tejeez/geckokapula/gecko_sdk_suite/v2.7/platform/Device/SiliconLabs/BGM1/Include/bgm1_adc.h

/***************************************************************************//**
 * @file
 * @brief BGM1_ADC register and bit field definitions
 *******************************************************************************
 * # License
 * <b>Copyright 2020 Silicon Laboratories Inc. www.silabs.com</b>
 *******************************************************************************
 *
 * SPDX-License-Identifier: Zlib
 *
 * The licensor of this software is Silicon Laboratories Inc.
 *
 * This software is provided 'as-is', without any express or implied
 * warranty. In no event will the authors be held liable for any damages
 * arising from the use of this software.
 *
 * Permission is granted to anyone to use this software for any purpose,
 * including commercial applications, and to alter it and redistribute it
 * freely, subject to the following restrictions:
 *
 * 1. The origin of this software must not be misrepresented; you must not
 *    claim that you wrote the original software. If you use this software
 *    in a product, an acknowledgment in the product documentation would be
 *    appreciated but is not required.
 * 2. Altered source versions must be plainly marked as such, and must not be
 *    misrepresented as being the original software.
 * 3. This notice may not be removed or altered from any source distribution.
 *
 ******************************************************************************/

#if defined(__ICCARM__)
#pragma system_include       /* Treat file as system include file. */
#elif defined(__ARMCC_VERSION) && (__ARMCC_VERSION >= 6010050)
#pragma clang system_header  /* Treat file as system include file. */
#endif

/***************************************************************************//**
 * @addtogroup Parts
 * @{
 ******************************************************************************/
/***************************************************************************//**
 * @defgroup BGM1_ADC ADC
 * @{
 * @brief BGM1_ADC Register Declaration
 ******************************************************************************/
/** ADC Register Declaration */
typedef struct {
  __IOM uint32_t CTRL;            /**< Control Register  */
  uint32_t       RESERVED0[1U];   /**< Reserved for future use **/
  __IOM uint32_t CMD;             /**< Command Register  */
  __IM uint32_t  STATUS;          /**< Status Register  */
  __IOM uint32_t SINGLECTRL;      /**< Single Channel Control Register  */
  __IOM uint32_t SINGLECTRLX;     /**< Single Channel Control Register Continued  */
  __IOM uint32_t SCANCTRL;        /**< Scan Control Register  */
  __IOM uint32_t SCANCTRLX;       /**< Scan Control Register Continued  */
  __IOM uint32_t SCANMASK;        /**< Scan Sequence Input Mask Register  */
  __IOM uint32_t SCANINPUTSEL;    /**< Input Selection Register for Scan Mode  */
  __IOM uint32_t SCANNEGSEL;      /**< Negative Input Select Register for Scan  */
  __IOM uint32_t CMPTHR;          /**< Compare Threshold Register  */
  __IOM uint32_t BIASPROG;        /**< Bias Programming Register for Various Analog Blocks Used in ADC Operation  */
  __IOM uint32_t CAL;             /**< Calibration Register  */
  __IM uint32_t  IF;              /**< Interrupt Flag Register  */
  __IOM uint32_t IFS;             /**< Interrupt Flag Set Register  */
  __IOM uint32_t IFC;             /**< Interrupt Flag Clear Register  */
  __IOM uint32_t IEN;             /**< Interrupt Enable Register  */
  __IM uint32_t  SINGLEDATA;      /**< Single Conversion Result Data  */
  __IM uint32_t  SCANDATA;        /**< Scan Conversion Result Data  */
  __IM uint32_t  SINGLEDATAP;     /**< Single Conversion Result Data Peek Register  */
  __IM uint32_t  SCANDATAP;       /**< Scan Sequence Result Data Peek Register  */
  uint32_t       RESERVED1[4U];   /**< Reserved for future use **/
  __IM uint32_t  SCANDATAX;       /**< Scan Sequence Result Data + Data Source Register  */
  __IM uint32_t  SCANDATAXP;      /**< Scan Sequence Result Data + Data Source Peek Register  */

  uint32_t       RESERVED2[3U];   /**< Reserved for future use **/
  __IM uint32_t  APORTREQ;        /**< APORT Request Status Register  */
  __IM uint32_t  APORTCONFLICT;   /**< APORT Conflict Status Register  */
  __IM uint32_t  SINGLEFIFOCOUNT; /**< Single FIFO Count Register  */
  __IM uint32_t  SCANFIFOCOUNT;   /**< Scan FIFO Count Register  */
  __IOM uint32_t SINGLEFIFOCLEAR; /**< Single FIFO Clear Register  */
  __IOM uint32_t SCANFIFOCLEAR;   /**< Scan FIFO Clear Register  */
  __IOM uint32_t APORTMASTERDIS;  /**< APORT Bus Master Disable Register  */
} ADC_TypeDef;                    /** @} */

/***************************************************************************//**
 * @addtogroup BGM1_ADC
 * @{
 * @defgroup BGM1_ADC_BitFields  ADC Bit Fields
 * @{
 ******************************************************************************/

/* Bit fields for ADC CTRL */
#define _ADC_CTRL_RESETVALUE                               0x001F0000UL                              /**< Default value for ADC_CTRL */
#define _ADC_CTRL_MASK                                     0x2F7F7FDFUL                              /**< Mask for ADC_CTRL */
#define _ADC_CTRL_WARMUPMODE_SHIFT                         0                                         /**< Shift value for ADC_WARMUPMODE */
#define _ADC_CTRL_WARMUPMODE_MASK                          0x3UL                                     /**< Bit mask for ADC_WARMUPMODE */
#define _ADC_CTRL_WARMUPMODE_DEFAULT                       0x00000000UL                              /**< Mode DEFAULT for ADC_CTRL */
#define _ADC_CTRL_WARMUPMODE_NORMAL                        0x00000000UL                              /**< Mode NORMAL for ADC_CTRL */
#define _ADC_CTRL_WARMUPMODE_KEEPINSTANDBY                 0x00000001UL                              /**< Mode KEEPINSTANDBY for ADC_CTRL */
#define _ADC_CTRL_WARMUPMODE_KEEPINSLOWACC                 0x00000002UL                              /**< Mode KEEPINSLOWACC for ADC_CTRL */
#define _ADC_CTRL_WARMUPMODE_KEEPADCWARM                   0x00000003UL                              /**< Mode KEEPADCWARM for ADC_CTRL */
#define ADC_CTRL_WARMUPMODE_DEFAULT                        (_ADC_CTRL_WARMUPMODE_DEFAULT << 0)       /**< Shifted mode DEFAULT for ADC_CTRL */
#define ADC_CTRL_WARMUPMODE_NORMAL                         (_ADC_CTRL_WARMUPMODE_NORMAL << 0)        /**< Shifted mode NORMAL for ADC_CTRL */
#define ADC_CTRL_WARMUPMODE_KEEPINSTANDBY                  (_ADC_CTRL_WARMUPMODE_KEEPINSTANDBY << 0) /**< Shifted mode KEEPINSTANDBY for ADC_CTRL */
#define ADC_CTRL_WARMUPMODE_KEEPINSLOWACC                  (_ADC_CTRL_WARMUPMODE_KEEPINSLOWACC << 0) /**< Shifted mode KEEPINSLOWACC for ADC_CTRL */
#define ADC_CTRL_WARMUPMODE_KEEPADCWARM                    (_ADC_CTRL_WARMUPMODE_KEEPADCWARM << 0)   /**< Shifted mode KEEPADCWARM for ADC_CTRL */
#define ADC_CTRL_SINGLEDMAWU                               (0x1UL << 2)                              /**< SINGLEFIFO DMA Wakeup */
#define _ADC_CTRL_SINGLEDMAWU_SHIFT                        2                                         /**< Shift value for ADC_SINGLEDMAWU */
#define _ADC_CTRL_SINGLEDMAWU_MASK                         0x4UL                                     /**< Bit mask for ADC_SINGLEDMAWU */
#define _ADC_CTRL_SINGLEDMAWU_DEFAULT                      0x00000000UL                              /**< Mode DEFAULT for ADC_CTRL */
#define ADC_CTRL_SINGLEDMAWU_DEFAULT                       (_ADC_CTRL_SINGLEDMAWU_DEFAULT << 2)      /**< Shifted mode DEFAULT for ADC_CTRL */
#define ADC_CTRL_SCANDMAWU                                 (0x1UL << 3)                              /**< SCANFIFO DMA Wakeup */
#define _ADC_CTRL_SCANDMAWU_SHIFT                          3                                         /**< Shift value for ADC_SCANDMAWU */
#define _ADC_CTRL_SCANDMAWU_MASK                           0x8UL                                     /**< Bit mask for ADC_SCANDMAWU */
#define _ADC_CTRL_SCANDMAWU_DEFAULT                        0x00000000UL                              /**< Mode DEFAULT for ADC_CTRL */
#define ADC_CTRL_SCANDMAWU_DEFAULT                         (_ADC_CTRL_SCANDMAWU_DEFAULT << 3)        /**< Shifted mode DEFAULT for ADC_CTRL */
#define ADC_CTRL_TAILGATE                                  (0x1UL << 4)                              /**< Conversion Tailgating */
#define _ADC_CTRL_TAILGATE_SHIFT                           4                                         /**< Shift value for ADC_TAILGATE */
#define _ADC_CTRL_TAILGATE_MASK                            0x10UL                                    /**< Bit mask for ADC_TAILGATE */
#define _ADC_CTRL_TAILGATE_DEFAULT                         0x00000000UL                              /**< Mode DEFAULT for ADC_CTRL */
#define ADC_CTRL_TAILGATE_DEFAULT                          (_ADC_CTRL_TAILGATE_DEFAULT << 4)         /**< Shifted mode DEFAULT for ADC_CTRL */
#define ADC_CTRL_ASYNCCLKEN                                (0x1UL << 6)                              /**< Selects ASYNC CLK Enable Mode When ADCCLKMODE=1 */
#define _ADC_CTRL_ASYNCCLKEN_SHIFT                         6                                         /**< Shift value for ADC_ASYNCCLKEN */
#define _ADC_CTRL_ASYNCCLKEN_MASK                          0x40UL                                    /**< Bit mask for ADC_ASYNCCLKEN */
#define _ADC_CTRL_ASYNCCLKEN_DEFAULT                       0x00000000UL                              /**< Mode DEFAULT for ADC_CTRL */
#define _ADC_CTRL_ASYNCCLKEN_ASNEEDED                      0x00000000UL                              /**< Mode ASNEEDED for ADC_CTRL */
#define _ADC_CTRL_ASYNCCLKEN_ALWAYSON                      0x00000001UL                              /**< Mode ALWAYSON for ADC_CTRL */
#define ADC_CTRL_ASYNCCLKEN_DEFAULT                        (_ADC_CTRL_ASYNCCLKEN_DEFAULT << 6)       /**< Shifted mode DEFAULT for ADC_CTRL */
#define ADC_CTRL_ASYNCCLKEN_ASNEEDED                       (_ADC_CTRL_ASYNCCLKEN_ASNEEDED << 6)      /**< Shifted mode ASNEEDED for ADC_CTRL */
#define ADC_CTRL_ASYNCCLKEN_ALWAYSON                       (_ADC_CTRL_ASYNCCLKEN_ALWAYSON << 6)      /**< Shifted mode ALWAYSON for ADC_CTRL */
#define ADC_CTRL_ADCCLKMODE                                (0x1UL << 7)                              /**< ADC Clock Mode */
#define _ADC_CTRL_ADCCLKMODE_SHIFT                         7                                         /**< Shift value for ADC_ADCCLKMODE */
#define _ADC_CTRL_ADCCLKMODE_MASK                          0x80UL                                    /**< Bit mask for ADC_ADCCLKMODE */
#define _ADC_CTRL_ADCCLKMODE_DEFAULT                       0x00000000UL                              /**< Mode DEFAULT for ADC_CTRL */
#define _ADC_CTRL_ADCCLKMODE_SYNC                          0x00000000UL                              /**< Mode SYNC for ADC_CTRL */
#define _ADC_CTRL_ADCCLKMODE_ASYNC                         0x00000001UL                              /**< Mode ASYNC for ADC_CTRL */
#define ADC_CTRL_ADCCLKMODE_DEFAULT                        (_ADC_CTRL_ADCCLKMODE_DEFAULT << 7)       /**< Shifted mode DEFAULT for ADC_CTRL */
#define ADC_CTRL_ADCCLKMODE_SYNC                           (_ADC_CTRL_ADCCLKMODE_SYNC << 7)          /**< Shifted mode SYNC for ADC_CTRL */
#define ADC_CTRL_ADCCLKMODE_ASYNC                          (_ADC_CTRL_ADCCLKMODE_ASYNC << 7)         /**< Shifted mode ASYNC for ADC_CTRL */
#define _ADC_CTRL_PRESC_SHIFT                              8                                         /**< Shift value for ADC_PRESC */
#define _ADC_CTRL_PRESC_MASK                               0x7F00UL                                  /**< Bit mask for ADC_PRESC */
#define _ADC_CTRL_PRESC_DEFAULT                            0x00000000UL                              /**< Mode DEFAULT for ADC_CTRL */
#define _ADC_CTRL_PRESC_NODIVISION                         0x00000000UL                              /**< Mode NODIVISION for ADC_CTRL */
#define ADC_CTRL_PRESC_DEFAULT                             (_ADC_CTRL_PRESC_DEFAULT << 8)            /**< Shifted mode DEFAULT for ADC_CTRL */
#define ADC_CTRL_PRESC_NODIVISION                          (_ADC_CTRL_PRESC_NODIVISION << 8)         /**< Shifted mode NODIVISION for ADC_CTRL */
#define _ADC_CTRL_TIMEBASE_SHIFT                           16                                        /**< Shift value for ADC_TIMEBASE */
#define _ADC_CTRL_TIMEBASE_MASK                            0x7F0000UL                                /**< Bit mask for ADC_TIMEBASE */
#define _ADC_CTRL_TIMEBASE_DEFAULT                         0x0000001FUL                              /**< Mode DEFAULT for ADC_CTRL */
#define ADC_CTRL_TIMEBASE_DEFAULT                          (_ADC_CTRL_TIMEBASE_DEFAULT << 16)        /**< Shifted mode DEFAULT for ADC_CTRL */
#define _ADC_CTRL_OVSRSEL_SHIFT                            24                                        /**< Shift value for ADC_OVSRSEL */
#define _ADC_CTRL_OVSRSEL_MASK                             0xF000000UL                               /**< Bit mask for ADC_OVSRSEL */
#define _ADC_CTRL_OVSRSEL_DEFAULT                          0x00000000UL                              /**< Mode DEFAULT for ADC_CTRL */
#define _ADC_CTRL_OVSRSEL_X2                               0x00000000UL                              /**< Mode X2 for ADC_CTRL */
#define _ADC_CTRL_OVSRSEL_X4                               0x00000001UL                              /**< Mode X4 for ADC_CTRL */
#define _ADC_CTRL_OVSRSEL_X8                               0x00000002UL                              /**< Mode X8 for ADC_CTRL */
#define _ADC_CTRL_OVSRSEL_X16                              0x00000003UL                              /**< Mode X16 for ADC_CTRL */
#define _ADC_CTRL_OVSRSEL_X32                              0x00000004UL                              /**< Mode X32 for ADC_CTRL */
#define _ADC_CTRL_OVSRSEL_X64                              0x00000005UL                              /**< Mode X64 for ADC_CTRL */
#define _ADC_CTRL_OVSRSEL_X128                             0x00000006UL                              /**< Mode X128 for ADC_CTRL */
#define _ADC_CTRL_OVSRSEL_X256                             0x00000007UL                              /**< Mode X256 for ADC_CTRL */
#define _ADC_CTRL_OVSRSEL_X512                             0x00000008UL                              /**< Mode X512 for ADC_CTRL */
#define _ADC_CTRL_OVSRSEL_X1024                            0x00000009UL                              /**< Mode X1024 for ADC_CTRL */
#define _ADC_CTRL_OVSRSEL_X2048                            0x0000000AUL                              /**< Mode X2048 for ADC_CTRL */
#define _ADC_CTRL_OVSRSEL_X4096                            0x0000000BUL                              /**< Mode X4096 for ADC_CTRL */
#define ADC_CTRL_OVSRSEL_DEFAULT                           (_ADC_CTRL_OVSRSEL_DEFAULT << 24)         /**< Shifted mode DEFAULT for ADC_CTRL */
#define ADC_CTRL_OVSRSEL_X2                                (_ADC_CTRL_OVSRSEL_X2 << 24)              /**< Shifted mode X2 for ADC_CTRL */
#define ADC_CTRL_OVSRSEL_X4                                (_ADC_CTRL_OVSRSEL_X4 << 24)              /**< Shifted mode X4 for ADC_CTRL */
#define ADC_CTRL_OVSRSEL_X8                                (_ADC_CTRL_OVSRSEL_X8 << 24)              /**< Shifted mode X8 for ADC_CTRL */
#define ADC_CTRL_OVSRSEL_X16                               (_ADC_CTRL_OVSRSEL_X16 << 24)             /**< Shifted mode X16 for ADC_CTRL */
#define ADC_CTRL_OVSRSEL_X32                               (_ADC_CTRL_OVSRSEL_X32 << 24)             /**< Shifted mode X32 for ADC_CTRL */
#define ADC_CTRL_OVSRSEL_X64                               (_ADC_CTRL_OVSRSEL_X64 << 24)             /**< Shifted mode X64 for ADC_CTRL */
#define ADC_CTRL_OVSRSEL_X128                              (_ADC_CTRL_OVSRSEL_X128 << 24)            /**< Shifted mode X128 for ADC_CTRL */
#define ADC_CTRL_OVSRSEL_X256                              (_ADC_CTRL_OVSRSEL_X256 << 24)            /**< Shifted mode X256 for ADC_CTRL */
#define ADC_CTRL_OVSRSEL_X512                              (_ADC_CTRL_OVSRSEL_X512 << 24)            /**< Shifted mode X512 for ADC_CTRL */
#define ADC_CTRL_OVSRSEL_X1024                             (_ADC_CTRL_OVSRSEL_X1024 << 24)           /**< Shifted mode X1024 for ADC_CTRL */
#define ADC_CTRL_OVSRSEL_X2048                             (_ADC_CTRL_OVSRSEL_X2048 << 24)           /**< Shifted mode X2048 for ADC_CTRL */
#define ADC_CTRL_OVSRSEL_X4096                             (_ADC_CTRL_OVSRSEL_X4096 << 24)           /**< Shifted mode X4096 for ADC_CTRL */
#define ADC_CTRL_CHCONMODE                                 (0x1UL << 29)                             /**< Channel Connect */
#define _ADC_CTRL_CHCONMODE_SHIFT                          29                                        /**< Shift value for ADC_CHCONMODE */
#define _ADC_CTRL_CHCONMODE_MASK                           0x20000000UL                              /**< Bit mask for ADC_CHCONMODE */
#define _ADC_CTRL_CHCONMODE_DEFAULT                        0x00000000UL                              /**< Mode DEFAULT for ADC_CTRL */
#define _ADC_CTRL_CHCONMODE_MAXSETTLE                      0x00000000UL                              /**< Mode MAXSETTLE for ADC_CTRL */
#define _ADC_CTRL_CHCONMODE_MAXRESP                        0x00000001UL                              /**< Mode MAXRESP for ADC_CTRL */
#define ADC_CTRL_CHCONMODE_DEFAULT                         (_ADC_CTRL_CHCONMODE_DEFAULT << 29)       /**< Shifted mode DEFAULT for ADC_CTRL */
#define ADC_CTRL_CHCONMODE_MAXSETTLE                       (_ADC_CTRL_CHCONMODE_MAXSETTLE << 29)     /**< Shifted mode MAXSETTLE for ADC_CTRL */
#define ADC_CTRL_CHCONMODE_MAXRESP                         (_ADC_CTRL_CHCONMODE_MAXRESP << 29)       /**< Shifted mode MAXRESP for ADC_CTRL */

/* Bit fields for ADC CMD */
#define _ADC_CMD_RESETVALUE                                0x00000000UL                        /**< Default value for ADC_CMD */
#define _ADC_CMD_MASK                                      0x0000000FUL                        /**< Mask for ADC_CMD */
#define ADC_CMD_SINGLESTART                                (0x1UL << 0)                        /**< Single Channel Conversion Start */
#define _ADC_CMD_SINGLESTART_SHIFT                         0                                   /**< Shift value for ADC_SINGLESTART */
#define _ADC_CMD_SINGLESTART_MASK                          0x1UL                               /**< Bit mask for ADC_SINGLESTART */
#define _ADC_CMD_SINGLESTART_DEFAULT                       0x00000000UL                        /**< Mode DEFAULT for ADC_CMD */
#define ADC_CMD_SINGLESTART_DEFAULT                        (_ADC_CMD_SINGLESTART_DEFAULT << 0) /**< Shifted mode DEFAULT for ADC_CMD */
#define ADC_CMD_SINGLESTOP                                 (0x1UL << 1)                        /**< Single Channel Conversion Stop */
#define _ADC_CMD_SINGLESTOP_SHIFT                          1                                   /**< Shift value for ADC_SINGLESTOP */
#define _ADC_CMD_SINGLESTOP_MASK                           0x2UL                               /**< Bit mask for ADC_SINGLESTOP */
#define _ADC_CMD_SINGLESTOP_DEFAULT                        0x00000000UL                        /**< Mode DEFAULT for ADC_CMD */
#define ADC_CMD_SINGLESTOP_DEFAULT                         (_ADC_CMD_SINGLESTOP_DEFAULT << 1)  /**< Shifted mode DEFAULT for ADC_CMD */
#define ADC_CMD_SCANSTART                                  (0x1UL << 2)                        /**< Scan Sequence Start */
#define _ADC_CMD_SCANSTART_SHIFT                           2                                   /**< Shift value for ADC_SCANSTART */
#define _ADC_CMD_SCANSTART_MASK                            0x4UL                               /**< Bit mask for ADC_SCANSTART */
#define _ADC_CMD_SCANSTART_DEFAULT                         0x00000000UL                        /**< Mode DEFAULT for ADC_CMD */
#define ADC_CMD_SCANSTART_DEFAULT                          (_ADC_CMD_SCANSTART_DEFAULT << 2)   /**< Shifted mode DEFAULT for ADC_CMD */
#define ADC_CMD_SCANSTOP                                   (0x1UL << 3)                        /**< Scan Sequence Stop */
#define _ADC_CMD_SCANSTOP_SHIFT                            3                                   /**< Shift value for ADC_SCANSTOP */
#define _ADC_CMD_SCANSTOP_MASK                             0x8UL                               /**< Bit mask for ADC_SCANSTOP */
#define _ADC_CMD_SCANSTOP_DEFAULT                          0x00000000UL                        /**< Mode DEFAULT for ADC_CMD */
#define ADC_CMD_SCANSTOP_DEFAULT                           (_ADC_CMD_SCANSTOP_DEFAULT << 3)    /**< Shifted mode DEFAULT for ADC_CMD */

/* Bit fields for ADC STATUS */
#define _ADC_STATUS_RESETVALUE                             0x00000000UL                             /**< Default value for ADC_STATUS */
#define _ADC_STATUS_MASK                                   0x00031F03UL                             /**< Mask for ADC_STATUS */
#define ADC_STATUS_SINGLEACT                               (0x1UL << 0)                             /**< Single Channel Conversion Active */
#define _ADC_STATUS_SINGLEACT_SHIFT                        0                                        /**< Shift value for ADC_SINGLEACT */
#define _ADC_STATUS_SINGLEACT_MASK                         0x1UL                                    /**< Bit mask for ADC_SINGLEACT */
#define _ADC_STATUS_SINGLEACT_DEFAULT                      0x00000000UL                             /**< Mode DEFAULT for ADC_STATUS */
#define ADC_STATUS_SINGLEACT_DEFAULT                       (_ADC_STATUS_SINGLEACT_DEFAULT << 0)     /**< Shifted mode DEFAULT for ADC_STATUS */
#define ADC_STATUS_SCANACT                                 (0x1UL << 1)                             /**< Scan Conversion Active */
#define _ADC_STATUS_SCANACT_SHIFT                          1                                        /**< Shift value for ADC_SCANACT */
#define _ADC_STATUS_SCANACT_MASK                           0x2UL                                    /**< Bit mask for ADC_SCANACT */
#define _ADC_STATUS_SCANACT_DEFAULT                        0x00000000UL                             /**< Mode DEFAULT for ADC_STATUS */
#define ADC_STATUS_SCANACT_DEFAULT                         (_ADC_STATUS_SCANACT_DEFAULT << 1)       /**< Shifted mode DEFAULT for ADC_STATUS */
#define ADC_STATUS_SINGLEREFWARM                           (0x1UL << 8)                             /**< Single Channel Reference Warmed Up */
#define _ADC_STATUS_SINGLEREFWARM_SHIFT                    8                                        /**< Shift value for ADC_SINGLEREFWARM */
#define _ADC_STATUS_SINGLEREFWARM_MASK                     0x100UL                                  /**< Bit mask for ADC_SINGLEREFWARM */
#define _ADC_STATUS_SINGLEREFWARM_DEFAULT                  0x00000000UL                             /**< Mode DEFAULT for ADC_STATUS */
#define ADC_STATUS_SINGLEREFWARM_DEFAULT                   (_ADC_STATUS_SINGLEREFWARM_DEFAULT << 8) /**< Shifted mode DEFAULT for ADC_STATUS */
#define ADC_STATUS_SCANREFWARM                             (0x1UL << 9)                             /**< Scan Reference Warmed Up */
#define _ADC_STATUS_SCANREFWARM_SHIFT                      9                                        /**< Shift value for ADC_SCANREFWARM */
#define _ADC_STATUS_SCANREFWARM_MASK                       0x200UL                                  /**< Bit mask for ADC_SCANREFWARM */
#define _ADC_STATUS_SCANREFWARM_DEFAULT                    0x00000000UL                             /**< Mode DEFAULT for ADC_STATUS */
#define ADC_STATUS_SCANREFWARM_DEFAULT                     (_ADC_STATUS_SCANREFWARM_DEFAULT << 9)   /**< Shifted mode DEFAULT for ADC_STATUS */
#define _ADC_STATUS_PROGERR_SHIFT                          10                                       /**< Shift value for ADC_PROGERR */
#define _ADC_STATUS_PROGERR_MASK                           0xC00UL                                  /**< Bit mask for ADC_PROGERR */
#define _ADC_STATUS_PROGERR_DEFAULT                        0x00000000UL                             /**< Mode DEFAULT for ADC_STATUS */
#define _ADC_STATUS_PROGERR_BUSCONF                        0x00000001UL                             /**< Mode BUSCONF for ADC_STATUS */
#define _ADC_STATUS_PROGERR_NEGSELCONF                     0x00000002UL                             /**< Mode NEGSELCONF for ADC_STATUS */
#define ADC_STATUS_PROGERR_DEFAULT                         (_ADC_STATUS_PROGERR_DEFAULT << 10)      /**< Shifted mode DEFAULT for ADC_STATUS */
#define ADC_STATUS_PROGERR_BUSCONF                         (_ADC_STATUS_PROGERR_BUSCONF << 10)      /**< Shifted mode BUSCONF for ADC_STATUS */
#define ADC_STATUS_PROGERR_NEGSELCONF                      (_ADC_STATUS_PROGERR_NEGSELCONF << 10)   /**< Shifted mode NEGSELCONF for ADC_STATUS */
#define ADC_STATUS_WARM                                    (0x1UL << 12)                            /**< ADC Warmed Up */
#define _ADC_STATUS_WARM_SHIFT                             12                                       /**< Shift value for ADC_WARM */
#define _ADC_STATUS_WARM_MASK                              0x1000UL                                 /**< Bit mask for ADC_WARM */
#define _ADC_STATUS_WARM_DEFAULT                           0x00000000UL                             /**< Mode DEFAULT for ADC_STATUS */
#define ADC_STATUS_WARM_DEFAULT                            (_ADC_STATUS_WARM_DEFAULT << 12)         /**< Shifted mode DEFAULT for ADC_STATUS */
#define ADC_STATUS_SINGLEDV                                (0x1UL << 16)                            /**< Single Channel Data Valid */
#define _ADC_STATUS_SINGLEDV_SHIFT                         16                                       /**< Shift value for ADC_SINGLEDV */
#define _ADC_STATUS_SINGLEDV_MASK                          0x10000UL                                /**< Bit mask for ADC_SINGLEDV */
#define _ADC_STATUS_SINGLEDV_DEFAULT                       0x00000000UL                             /**< Mode DEFAULT for ADC_STATUS */
#define ADC_STATUS_SINGLEDV_DEFAULT                        (_ADC_STATUS_SINGLEDV_DEFAULT << 16)     /**< Shifted mode DEFAULT for ADC_STATUS */
#define ADC_STATUS_SCANDV                                  (0x1UL << 17)                            /**< Scan Data Valid */
#define _ADC_STATUS_SCANDV_SHIFT                           17                                       /**< Shift value for ADC_SCANDV */
#define _ADC_STATUS_SCANDV_MASK                            0x20000UL                                /**< Bit mask for ADC_SCANDV */
#define _ADC_STATUS_SCANDV_DEFAULT                         0x00000000UL                             /**< Mode DEFAULT for ADC_STATUS */
#define ADC_STATUS_SCANDV_DEFAULT                          (_ADC_STATUS_SCANDV_DEFAULT << 17)       /**< Shifted mode DEFAULT for ADC_STATUS */

/* Bit fields for ADC SINGLECTRL */
#define _ADC_SINGLECTRL_RESETVALUE                         0x00FFFF00UL                               /**< Default value for ADC_SINGLECTRL */
#define _ADC_SINGLECTRL_MASK                               0xAFFFFFFFUL                               /**< Mask for ADC_SINGLECTRL */
#define ADC_SINGLECTRL_REP                                 (0x1UL << 0)                               /**< Single Channel Repetitive Mode */
#define _ADC_SINGLECTRL_REP_SHIFT                          0                                          /**< Shift value for ADC_REP */
#define _ADC_SINGLECTRL_REP_MASK                           0x1UL                                      /**< Bit mask for ADC_REP */
#define _ADC_SINGLECTRL_REP_DEFAULT                        0x00000000UL                               /**< Mode DEFAULT for ADC_SINGLECTRL */
#define ADC_SINGLECTRL_REP_DEFAULT                         (_ADC_SINGLECTRL_REP_DEFAULT << 0)         /**< Shifted mode DEFAULT for ADC_SINGLECTRL */
#define ADC_SINGLECTRL_DIFF                                (0x1UL << 1)                               /**< Single Channel Differential Mode */
#define _ADC_SINGLECTRL_DIFF_SHIFT                         1                                          /**< Shift value for ADC_DIFF */
#define _ADC_SINGLECTRL_DIFF_MASK                          0x2UL                                      /**< Bit mask for ADC_DIFF */
#define _ADC_SINGLECTRL_DIFF_DEFAULT                       0x00000000UL                               /**< Mode DEFAULT for ADC_SINGLECTRL */
#define ADC_SINGLECTRL_DIFF_DEFAULT                        (_ADC_SINGLECTRL_DIFF_DEFAULT << 1)        /**< Shifted mode DEFAULT for ADC_SINGLECTRL */
#define ADC_SINGLECTRL_ADJ                                 (0x1UL << 2)                               /**< Single Channel Result Adjustment */
#define _ADC_SINGLECTRL_ADJ_SHIFT                          2                                          /**< Shift value for ADC_ADJ */
#define _ADC_SINGLECTRL_ADJ_MASK                           0x4UL                                      /**< Bit mask for ADC_ADJ */
#define _ADC_SINGLECTRL_ADJ_DEFAULT                        0x00000000UL                               /**< Mode DEFAULT for ADC_SINGLECTRL */
#define _ADC_SINGLECTRL_ADJ_RIGHT                          0x00000000UL                               /**< Mode RIGHT for ADC_SINGLECTRL */
#define _ADC_SINGLECTRL_ADJ_LEFT                           0x00000001UL                               /**< Mode LEFT for ADC_SINGLECTRL */
#define ADC_SINGLECTRL_ADJ_DEFAULT                         (_ADC_SINGLECTRL_ADJ_DEFAULT << 2)         /**< Shifted mode DEFAULT for ADC_SINGLECTRL */
#define ADC_SINGLECTRL_ADJ_RIGHT                           (_ADC_SINGLECTRL_ADJ_RIGHT << 2)           /**< Shifted mode RIGHT for ADC_SINGLECTRL */
#define ADC_SINGLECTRL_ADJ_LEFT                            (_ADC_SINGLECTRL_ADJ_LEFT << 2)            /**< Shifted mode LEFT for ADC_SINGLECTRL */
#define _ADC_SINGLECTRL_RES_SHIFT                          3                                          /**< Shift value for ADC_RES */
#define _ADC_SINGLECTRL_RES_MASK                           0x18UL                                     /**< Bit mask for ADC_RES */
#define _ADC_SINGLECTRL_RES_DEFAULT                        0x00000000UL                               /**< Mode DEFAULT for ADC_SINGLECTRL */
#define _ADC_SINGLECTRL_RES_12BIT                          0x00000000UL                               /**< Mode 12BIT for ADC_SINGLECTRL */
#define _ADC_SINGLECTRL_RES_8BIT                           0x00000001UL                               /**< Mode 8BIT for ADC_SINGLECTRL */
#define _ADC_SINGLECTRL_RES_6BIT                           0x00000002UL                               /**< Mode 6BIT for ADC_SINGLECTRL */
#define _ADC_SINGLECTRL_RES_OVS                            0x00000003UL                               /**< Mode OVS for ADC_SINGLECTRL */
#define ADC_SINGLECTRL_RES_DEFAULT                         (_ADC_SINGLECTRL_RES_DEFAULT << 3)         /**< Shifted mode DEFAULT for ADC_SINGLECTRL */
#define ADC_SINGLECTRL_RES_12BIT                           (_ADC_SINGLECTRL_RES_12BIT << 3)           /**< Shifted mode 12BIT for ADC_SINGLECTRL */
#define ADC_SINGLECTRL_RES_8BIT                            (_ADC_SINGLECTRL_RES_8BIT << 3)            /**< Shifted mode 8BIT for ADC_SINGLECTRL */
#define ADC_SINGLECTRL_RES_6BIT                            (_ADC_SINGLECTRL_RES_6BIT << 3)            /**< Shifted mode 6BIT for ADC_SINGLECTRL */
#define ADC_SINGLECTRL_RES_OVS                             (_ADC_SINGLECTRL_RES_OVS << 3)             /**< Shifted mode OVS for ADC_SINGLECTRL */
#define _ADC_SINGLECTRL_REF_SHIFT                          5                                          /**< Shift value for ADC_REF */
#define _ADC_SINGLECTRL_REF_MASK                           0xE0UL                                     /**< Bit mask for ADC_REF */
#define _ADC_SINGLECTRL_REF_DEFAULT                        0x00000000UL                               /**< Mode DEFAULT for ADC_SINGLECTRL */
#define _ADC_SINGLECTRL_REF_1V25                           0x00000000UL                               /**< Mode 1V25 for ADC_SINGLECTRL */
#define _ADC_SINGLECTRL_REF_2V5                            0x00000001UL                               /**< Mode 2V5 for ADC_SINGLECTRL */
#define _ADC_SINGLECTRL_REF_VDD                            0x00000002UL                               /**< Mode VDD for ADC_SINGLECTRL */
#define _ADC_SINGLECTRL_REF_5V                             0x00000003UL                               /**< Mode 5V for ADC_SINGLECTRL */
#define _ADC_SINGLECTRL_REF_EXTSINGLE                      0x00000004UL                               /**< Mode EXTSINGLE for ADC_SINGLECTRL */
#define _ADC_SINGLECTRL_REF_2XEXTDIFF                      0x00000005UL                               /**< Mode 2XEXTDIFF for ADC_SINGLECTRL */
#define _ADC_SINGLECTRL_REF_2XVDD                          0x00000006UL                               /**< Mode 2XVDD for ADC_SINGLECTRL */
#define _ADC_SINGLECTRL_REF_CONF                           0x00000007UL                               /**< Mode CONF for ADC_SINGLECTRL */
#define ADC_SINGLECTRL_REF_DEFAULT                         (_ADC_SINGLECTRL_REF_DEFAULT << 5)         /**< Shifted mode DEFAULT for ADC_SINGLECTRL */
#define ADC_SINGLECTRL_REF_1V25                            (_ADC_SINGLECTRL_REF_1V25 << 5)            /**< Shifted mode 1V25 for ADC_SINGLECTRL */
#define ADC_SINGLECTRL_REF_2V5                             (_ADC_SINGLECTRL_REF_2V5 << 5)             /**< Shifted mode 2V5 for ADC_SINGLECTRL */
#define ADC_SINGLECTRL_REF_VDD                             (_ADC_SINGLECTRL_REF_VDD << 5)             /**< Shifted mode VDD for ADC_SINGLECTRL */
#define ADC_SINGLECTRL_REF_5V                              (_ADC_SINGLECTRL_REF_5V << 5)              /**< Shifted mode 5V for ADC_SINGLECTRL */
#define ADC_SINGLECTRL_REF_EXTSINGLE                       (_ADC_SINGLECTRL_REF_EXTSINGLE << 5)       /**< Shifted mode EXTSINGLE for ADC_SINGLECTRL */
#define ADC_SINGLECTRL_REF_2XEXTDIFF                       (_ADC_SINGLECTRL_REF_2XEXTDIFF << 5)       /**< Shifted mode 2XEXTDIFF for ADC_SINGLECTRL */
#define ADC_SINGLECTRL_REF_2XVDD                           (_ADC_SINGLECTRL_REF_2XVDD << 5)           /**< Shifted mode 2XVDD for ADC_SINGLECTRL */
#define ADC_SINGLECTRL_REF_CONF                            (_ADC_SINGLECTRL_REF_CONF << 5)            /**< Shifted mode CONF for ADC_SINGLECTRL */
#define _ADC_SINGLECTRL_POSSEL_SHIFT                       8                                          /**< Shift value for ADC_POSSEL */
#define _ADC_SINGLECTRL_POSSEL_MASK                        0xFF00UL                                   /**< Bit mask for ADC_POSSEL */
#define _ADC_SINGLECTRL_POSSEL_APORT0XCH0                  0x00000000UL                               /**< Mode APORT0XCH0 for ADC_SINGLECTRL */
#define _ADC_SINGLECTRL_POSSEL_APORT0XCH1                  0x00000001UL                               /**< Mode APORT0XCH1 for ADC_SINGLECTRL */
#define _ADC_SINGLECTRL_POSSEL_APORT0XCH2                  0x00000002UL                               /**< Mode APORT0XCH2 for ADC_SINGLECTRL */
#define _ADC_SINGLECTRL_POSSEL_APORT0XCH3                  0x00000003UL                               /**< Mode APORT0XCH3 for ADC_SINGLECTRL */
#define _ADC_SINGLECTRL_POSSEL_APORT0XCH4                  0x00000004UL                               /**< Mode APORT0XCH4 for ADC_SINGLECTRL */
#define _ADC_SINGLECTRL_POSSEL_APORT0XCH5                  0x00000005UL                               /**< Mode APORT0XCH5 for ADC_SINGLECTRL */
#define _ADC_SINGLECTRL_POSSEL_APORT0XCH6                  0x00000006UL                               /**< Mode APORT0XCH6 for ADC_SINGLECTRL */
#define _ADC_SINGLECTRL_POSSEL_APORT0XCH7                  0x00000007UL                               /**< Mode APORT0XCH7 for ADC_SINGLECTRL */
#define _ADC_SINGLECTRL_POSSEL_APORT0XCH8                  0x00000008UL                               /**< Mode APORT0XCH8 for ADC_SINGLECTRL */
#define _ADC_SINGLECTRL_POSSEL_APORT0XCH9                  0x00000009UL                               /**< Mode APORT0XCH9 for ADC_SINGLECTRL */
#define _ADC_SINGLECTRL_POSSEL_APORT0XCH10                 0x0000000AUL                               /**< Mode APORT0XCH10 for ADC_SINGLECTRL */
#define _ADC_SINGLECTRL_POSSEL_APORT0XCH11                 0x0000000BUL                               /**< Mode APORT0XCH11 for ADC_SINGLECTRL */
#define _ADC_SINGLECTRL_POSSEL_APORT0XCH12                 0x0000000CUL                               /**< Mode APORT0XCH12 for ADC_SINGLECTRL */
#define _ADC_SINGLECTRL_POSSEL_APORT0XCH13                 0x0000000DUL                               /**< Mode APORT0XCH13 for ADC_SINGLECTRL */
#define _ADC_SINGLECTRL_POSSEL_APORT0XCH14                 0x0000000EUL                               /**< Mode APORT0XCH14 for ADC_SINGLECTRL */
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
#define _ADC_SINGLECTRL_POSSEL_PAVDD                       0x000000E3UL                               /**< Mode PAVDD for ADC_SINGLECTRL */
#define _ADC_SINGLECTRL_POSSEL_DECOUPLE                    0x000000E4UL                               /**< Mode DECOUPLE for ADC_SINGLECTRL */
#define _ADC_SINGLECTRL_POSSEL_IOVDD                       0x000000E5UL                               /**< Mode IOVDD for ADC_SINGLECTRL */
#define _ADC_SINGLECTRL_POSSEL_IOVDD1                      0x000000E6UL                               /**< Mode IOVDD1 for ADC_SINGLECTRL */
#define _ADC_SINGLECTRL_POSSEL_VSP                         0x000000E7UL                               /**< Mode VSP for ADC_SINGLECTRL */
#define _ADC_SINGLECTRL_POSSEL_OPA2                        0x000000F2UL                               /**< Mode OPA2 for ADC_SINGLECTRL */
#define _ADC_SINGLECTRL_POSSEL_TEMP                        0x000000F3UL                               /**< Mode TEMP for ADC_SINGLECTRL */
#define _ADC_SINGLECTRL_POSSEL_DAC0OUT0                    0x000000F4UL                               /**< Mode DAC0OUT0 for ADC_SINGLECTRL */
#define _ADC_SINGLECTRL_POSSEL_R5VOUT                      0x000000F5UL                               /**< Mode R5VOUT for ADC_SINGLECTRL */
#define _ADC_SINGLECTRL_POSSEL_SP1                         0x000000F6UL                               /**< Mode SP1 for ADC_SINGLECTRL */
#define _ADC_SINGLECTRL_POSSEL_SP2                         0x000000F7UL                               /**< Mode SP2 for ADC_SINGLECTRL */
#define _ADC_SINGLECTRL_POSSEL_DAC0OUT1                    0x000000F8UL                               /**< Mode DAC0OUT1 for ADC_SINGLECTRL */
#define _ADC_SINGLECTRL_POSSEL_SUBLSB                      0x000000F9UL                               /**< Mode SUBLSB for ADC_SINGLECTRL */
#define _ADC_SINGLECTRL_POSSEL_OPA3                        0x000000FAUL                               /**< Mode OPA3 for ADC_SINGLECTRL */
#define _ADC_SINGLECTRL_POSSEL_DEFAULT                     0x000000FFUL                               /**< Mode DEFAULT for ADC_SINGLECTRL */
#define _ADC_SINGLECTRL_POSSEL_VSS                         0x000000FFUL                               /**< Mode VSS for ADC_SINGLECTRL */
#define ADC_SINGLECTRL_POSSEL_APORT0XCH0                   (_ADC_SINGLECTRL_POSSEL_APORT0XCH0 << 8)   /**< Shifted mode APORT0XCH0 for ADC_SINGLECTRL */
#define ADC_SINGLECTRL_POSSEL_APORT0XCH1                   (_ADC_SINGLECTRL_POSSEL_APORT0XCH1 << 8)   /**< Shifted mode APORT0XCH1 for ADC_SINGLECTRL */
#define ADC_SINGLECTRL_POSSEL_APORT0XCH2                   (_ADC_SINGLECTRL_POSSEL_APORT0XCH2 << 8)   /**< Shifted mode APORT0XCH2 for ADC_SINGLECTRL */
#define ADC_SINGLECTRL_POSSEL_APORT0XCH3                   (_ADC_SINGLECTRL_POSSEL_APORT0XCH3 << 8)   /**< Shifted mode APORT0XCH3 for ADC_SINGLECTRL */
#define ADC_SINGLECTRL_POSSEL_APORT0XCH4                   (_ADC_SINGLECTRL_POSSEL_APORT0XCH4 << 8)   /**< Shifted mode APORT0XCH4 for ADC_SINGLECTRL */
#define ADC_SINGLECTRL_POSSEL_APORT0XCH5                   (_ADC_SINGLECTRL_POSSEL_APORT0XCH5 << 8)   /**< Shifted mode APORT0XCH5 for ADC_SINGLECTRL */
#define ADC_SINGLECTRL_POSSEL_APORT0XCH6                   (_ADC_SINGLECTRL_POSSEL_APORT0XCH6 << 8)   /**< Shifted mode APORT0XCH6 for ADC_SINGLECTRL */
#define ADC_SINGLECTRL_POSSEL_APORT0XCH7                   (_ADC_SINGLECTRL_POSSEL_APORT0XCH7 << 8)   /**< Shifted mode APORT0XCH7 for ADC_SINGLECTRL */
#define ADC_SINGLECTRL_POSSEL_APORT0XCH8                   (_ADC_SINGLECTRL_POSSEL_APORT0XCH8 << 8)   /**< Shifted mode APORT0XCH8 for ADC_SINGLECTRL */
#define ADC_SINGLECTRL_POSSEL_APORT0XCH9                   (_ADC_SINGLECTRL_POSSEL_APORT0XCH9 << 8)   /**< Shifted mode APORT0XCH9 for ADC_SINGLECTRL */
#define ADC_SINGLECTRL_POSSEL_APORT0XCH10                  (_ADC_SINGLECTRL_POSSEL_APORT0XCH10 << 8)  /**< Shifted mode APORT0XCH10 for ADC_SINGLECTRL */
#define ADC_SINGLECTRL_POSSEL_APORT0XCH11                  (_ADC_SINGLECTRL_POSSEL_APORT0XCH11 << 8)  /**< Shifted mode APORT0XCH11 for ADC_SINGLECTRL */
#define ADC_SINGLECTRL_POSSEL_APORT0XCH12                  (_ADC_SINGLECTRL_POSSEL_APORT0XCH12 << 8)  /**< Shifted mode APORT0XCH12 for ADC_SINGLECTRL */
#define ADC_SINGLECTRL_POSSEL_APORT0XCH13                  (_ADC_SINGLECTRL_POSSEL_APORT0XCH13 << 8)  /**< Shifted mode APORT0XCH13 for ADC_SINGLECTRL */
#define ADC_SINGLECTRL_POSSEL_APORT0XCH14                  (_ADC_SINGLECTRL_POSSEL_APORT0XCH14 << 8)  /**< Shifted mode APORT0XCH14 for ADC_SINGLECTRL */
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
#define ADC_SINGLECTRL_POSSEL_APORT4XCH29                  (_ADC_SINGLECTRL_POSSEL_APORT4XCH29 << 8)  /**< Shifted mode APORT4XCH29 for ADC_SINGLECTRL */
#define ADC_SINGLECTRL_POSSEL_APORT4YCH30                  (_ADC_SINGLECTRL_POSSEL_APORT4YCH30 << 8)  /**< Shifted mode APORT4YCH30 for ADC_SINGLECTRL */
#define ADC_SINGLECTRL_POSSEL_APORT4XCH31                  (_ADC_SINGLECTRL_POSSEL_APORT4XCH31 << 8)  /**< Shifted mode APORT4XCH31 for ADC_SINGLECTRL */
#define ADC_SINGLECTRL_POSSEL_AVDD                         (_ADC_SINGLECTRL_POSSEL_AVDD << 8)         /**< Shifted mode AVDD for ADC_SINGLECTRL */
#define ADC_SINGLECTRL_POSSEL_BUVDD                        (_ADC_SINGLECTRL_POSSEL_BUVDD << 8)        /**< Shifted mode BUVDD for ADC_SINGLECTRL */
#define ADC_SINGLECTRL_POSSEL_DVDD                         (_ADC_SINGLECTRL_POSSEL_DVDD << 8)         /**< Shifted mode DVDD for ADC_SINGLECTRL */
#define ADC_SINGLECTRL_POSSEL_PAVDD                        (_ADC_SINGLECTRL_POSSEL_PAVDD << 8)        /**< Shifted mode PAVDD for ADC_SINGLECTRL */
#define ADC_SINGLECTRL_POSSEL_DECOUPLE                     (_ADC_SINGLECTRL_POSSEL_DECOUPLE << 8)     /**< Shifted mode DECOUPLE for ADC_SINGLECTRL */
#define ADC_SINGLECTRL_POSSEL_IOVDD                        (_ADC_SINGLECTRL_POSSEL_IOVDD << 8)        /**< Shifted mode IOVDD for ADC_SINGLECTRL */
#define ADC_SINGLECTRL_POSSEL_IOVDD1                       (_ADC_SINGLECTRL_POSSEL_IOVDD1 << 8)       /**< Shifted mode IOVDD1 for ADC_SINGLECTRL */
#define ADC_SINGLECTRL_POSSEL_VSP                          (_ADC_SINGLECTRL_POSSEL_VSP << 8)          /**< Shifted mode VSP for ADC_SINGLECTRL */
#define ADC_SINGLECTRL_POSSEL_OPA2                         (_ADC_SINGLECTRL_POSSEL_OPA2 << 8)         /**< Shifted mode OPA2 for ADC_SINGLECTRL */
#define ADC_SINGLECTRL_POSSEL_TEMP                         (_ADC_SINGLECTRL_POSSEL_TEMP << 8)         /**< Shifted mode TEMP for ADC_SINGLECTRL */
#define ADC_SINGLECTRL_POSSEL_DAC0OUT0                     (_ADC_SINGLECTRL_POSSEL_DAC0OUT0 << 8)     /**< Shifted mode DAC0OUT0 for ADC_SINGLECTRL */
#define ADC_SINGLECTRL_POSSEL_R5VOUT                       (_ADC_SINGLECTRL_POSSEL_R5VOUT << 8)       /**< Shifted mode R5VOUT for ADC_SINGLECTRL */
#define ADC_SINGLECTRL_POSSEL_SP1                          (_ADC_SINGLECTRL_POSSEL_SP1 << 8)          /**< Shifted mode SP1 for ADC_SINGLECTRL */
#define ADC_SINGLECTRL_POSSEL_SP2                          (_ADC_SINGLECTRL_POSSEL_SP2 << 8)          /**< Shifted mode SP2 for ADC_SINGLECTRL */
#define ADC_SINGLECTRL_POSSEL_DAC0OUT1                     (_ADC_SINGLECTRL_POSSEL_DAC0OUT1 << 8)     /**< Shifted mode DAC0OUT1 for ADC_SINGLECTRL */
#define ADC_SINGLECTRL_POSSEL_SUBLSB                       (_ADC_SINGLECTRL_POSSEL_SUBLSB << 8)       /**< Shifted mode SUBLSB for ADC_SINGLECTRL */
#define ADC_SINGLECTRL_POSSEL_OPA3                         (_ADC_SINGLECTRL_POSSEL_OPA3 << 8)         /**< Shifted mode OPA3 for ADC_SINGLECTRL */
#define ADC_SINGLECTRL_POSSEL_DEFAULT                      (_ADC_SINGLECTRL_POSSEL_DEFAULT << 8)      /**< Shifted mode DEFAULT for ADC_SINGLECTRL */
#define ADC_SINGLECTRL_POSSEL_VSS                          (_ADC_SINGLECTRL_POSSEL_VSS << 8)          /**< Shifted mode VSS for ADC_SINGLECTRL */
#define _ADC_SINGLECTRL_NEGSEL_SHIFT                       16                                         /**< Shift value for ADC_NEGSEL */
#define _ADC_SINGLECTRL_NEGSEL_MASK                        0xFF0000UL                                 /**< Bit mask for ADC_NEGSEL */
#define _ADC_SINGLECTRL_NEGSEL_APORT0XCH0                  0x00000000UL                               /**< Mode APORT0XCH0 for ADC_SINGLECTRL */
#define _ADC_SINGLECTRL_NEGSEL_APORT0XCH1                  0x00000001UL                               /**< Mode APORT0XCH1 for ADC_SINGLECTRL */
#define _ADC_SINGLECTRL_NEGSEL_APORT0XCH2                  0x00000002UL                               /**< Mode APORT0XCH2 for ADC_SINGLECTRL */
#define _ADC_SINGLECTRL_NEGSEL_APORT0XCH3                  0x00000003UL                               /**< Mode APORT0XCH3 for ADC_SINGLECTRL */
#define _ADC_SINGLECTRL_NEGSEL_APORT0XCH4                  0x00000004UL                               /**< Mode APORT0XCH4 for ADC_SINGLECTRL */
#define _ADC_SINGLECTRL_NEGSEL_APORT0XCH5                  0x00000005UL                               /**< Mode APORT0XCH5 for ADC_SINGLECTRL */
#define _ADC_SINGLECTRL_NEGSEL_APORT0XCH6                  0x00000006UL                               /**< Mode APORT0XCH6 for ADC_SINGLECTRL */
#define _ADC_SINGLECTRL_NEGSEL_APORT0XCH7                  0x00000007UL                               /**< Mode APORT0XCH7 for ADC_SINGLECTRL */
#define _ADC_SINGLECTRL_NEGSEL_APORT0XCH8                  0x00000008UL                               /**< Mode APORT0XCH8 for ADC_SINGLECTRL */
#define _ADC_SINGLECTRL_NEGSEL_APORT0XCH9                  0x00000009UL                               /**< Mode APORT0XCH9 for ADC_SINGLECTRL */
#define _ADC_SINGLECTRL_NEGSEL_APORT0XCH10                 0x0000000AUL                               /**< Mode APORT0XCH10 for ADC_SINGLECTRL */
#define _ADC_SINGLECTRL_NEGSEL_APORT0XCH11                 0x0000000BUL                               /**< Mode APORT0XCH11 for ADC_SINGLECTRL */
#define _ADC_SINGLECTRL_NEGSEL_APORT0XCH12                 0x0000000CUL                               /**< Mode APORT0XCH12 for ADC_SINGLECTRL */
#define _ADC_SINGLECTRL_NEGSEL_APORT0XCH13                 0x0000000DUL                               /**< Mode APORT0XCH13 for ADC_SINGLECTRL */
#define _ADC_SINGLECTRL_NEGSEL_APORT0XCH14                 0x0000000EUL                               /**< Mode APORT0XCH14 for ADC_SINGLECTRL */
#define _ADC_SINGLECTRL_NEGSEL_APORT0XCH15                 0x0000000FUL                               /**< Mode APORT0XCH15 for ADC_SINGLECTRL */
#define _ADC_SINGLECTRL_NEGSEL_APORT0YCH0                  0x00000010UL                               /**< Mode APORT0YCH0 for ADC_SINGLECTRL */
#define _ADC_SINGLECTRL_NEGSEL_APORT0YCH1                  0x00000011UL                               /**< Mode APORT0YCH1 for ADC_SINGLECTRL */
#define _ADC_SINGLECTRL_NEGSEL_APORT0YCH2                  0x00000012UL                               /**< Mode APORT0YCH2 for ADC_SINGLECTRL */
#define _ADC_SINGLECTRL_NEGSEL_APORT0YCH3                  0x00000013UL                               /**< Mode APORT0YCH3 for ADC_SINGLECTRL */
#define _ADC_SINGLECTRL_NEGSEL_APORT0YCH4                  0x00000014UL                               /**< Mode APORT0YCH4 for ADC_SINGLECTRL */
#define _ADC_SINGLECTRL_NEGSEL_APORT0YCH5                  0x00000015UL                               /**< Mode APORT0YCH5 for ADC_SINGLECTRL */
#define _ADC_SINGLECTRL_NEGSEL_APORT0YCH6                  0x00000016UL                               /**< Mode APORT0YCH6 for ADC_SINGLECTRL */
#define _ADC_SINGLECTRL_NEGSEL_APORT0YCH7                  0x00000017UL                               /**< Mode APORT0YCH7 for ADC_SINGLECTRL */
#define _ADC_SINGLECTRL_NEGSEL_APORT0YCH8                  0x00000018UL                               /**< Mode APORT0YCH8 for ADC_SINGLECTRL */
#define _ADC_SINGLECTRL_NEGSEL_APORT0YCH9                  0x00000019UL                               /**< Mode APORT0YCH9 for ADC_SINGLECTRL */
#define _ADC_SINGLECTRL_NEGSEL_APORT0YCH10                 0x0000001AUL                               /**< Mode APORT0YCH10 for ADC_SINGLECTRL */
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
#define _ADC_SINGLECTRL_NEGSEL_APORT4XCH27                 0x0000009BUL                               /**< Mode APORT4XCH27 for ADC_SINGLECTRL */
#define _ADC_SINGLECTRL_NEGSEL_APORT4YCH28                 0x0000009CUL                               /**< Mode APORT4YCH28 for ADC_SINGLECTRL */
#define _ADC_SINGLECTRL_NEGSEL_APORT4XCH29                 0x0000009DUL                               /**< Mode APORT4XCH29 for ADC_SINGLECTRL */
#define _ADC_SINGLECTRL_NEGSEL_APORT4YCH30                 0x0000009EUL                               /**< Mode APORT4YCH30 for ADC_SINGLECTRL */
#define _ADC_SINGLECTRL_NEGSEL_APORT4XCH31                 0x0000009FUL                               /**< Mode APORT4XCH31 for ADC_SINGLECTRL */
#define _ADC_SINGLECTRL_NEGSEL_TESTN                       0x000000F5UL                               /**< Mode TESTN for ADC_SINGLECTRL */
#define _ADC_SINGLECTRL_NEGSEL_DEFAULT                     0x000000FFUL                               /**< Mode DEFAULT for ADC_SINGLECTRL */
#define _ADC_SINGLECTRL_NEGSEL_VSS                         0x000000FFUL                               /**< Mode VSS for ADC_SINGLECTRL */
#define ADC_SINGLECTRL_NEGSEL_APORT0XCH0                   (_ADC_SINGLECTRL_NEGSEL_APORT0XCH0 << 16)  /**< Shifted mode APORT0XCH0 for ADC_SINGLECTRL */
#define ADC_SINGLECTRL_NEGSEL_APORT0XCH1                   (_ADC_SINGLECTRL_NEGSEL_APORT0XCH1 << 16)  /**< Shifted mode APORT0XCH1 for ADC_SINGLECTRL */
#define ADC_SINGLECTRL_NEGSEL_APORT0XCH2                   (_ADC_SINGLECTRL_NEGSEL_APORT0XCH2 << 16)  /**< Shifted mode APORT0XCH2 for ADC_SINGLECTRL */
#define ADC_SINGLECTRL_NEGSEL_APORT0XCH3                   (_ADC_SINGLECTRL_NEGSEL_APORT0XCH3 << 16)  /**< Shifted mode APORT0XCH3 for ADC_SINGLECTRL */
#define ADC_SINGLECTRL_NEGSEL_APORT0XCH4                   (_ADC_SINGLECTRL_NEGSEL_APORT0XCH4 << 16)  /**< Shifted mode APORT0XCH4 for ADC_SINGLECTRL */
#define ADC_SINGLECTRL_NEGSEL_APORT0XCH5                   (_ADC_SINGLECTRL_NEGSEL_APORT0XCH5 << 16)  /**< Shifted mode APORT0XCH5 for ADC_SINGLECTRL */
#define ADC_SINGLECTRL_NEGSEL_APORT0XCH6                   (_ADC_SINGLECTRL_NEGSEL_APORT0XCH6 << 16)  /**< Shifted mode APORT0XCH6 for ADC_SINGLECTRL */
#define ADC_SINGLECTRL_NEGSEL_APORT0XCH7                   (_ADC_SINGLECTRL_NEGSEL_APORT0XCH7 << 16)  /**< Shifted mode APORT0XCH7 for ADC_SINGLECTRL */
#define ADC_SINGLECTRL_NEGSEL_APORT0XCH8                   (_ADC_SINGLECTRL_NEGSEL_APORT0XCH8 << 16)  /**< Shifted mode APORT0XCH8 for ADC_SINGLECTRL */
#define ADC_SINGLECTRL_NEGSEL_APORT0XCH9                   (_ADC_SINGLECTRL_NEGSEL_APORT0XCH9 << 16)  /**< Shifted mode APORT0XCH9 for ADC_SINGLECTRL */
#define ADC_SINGLECTRL_NEGSEL_APORT0XCH10                  (_ADC_SINGLECTRL_NEGSEL_APORT0XCH10 << 16) /**< Shifted mode APORT0XCH10 for ADC_SINGLECTRL */
#define ADC_SINGLECTRL_NEGSEL_APORT0XCH11                  (_ADC_SINGLECTRL_NEGSEL_APORT0XCH11 << 16) /**< Shifted mode APORT0XCH11 for ADC_SINGLECTRL */
#define ADC_SINGLECTRL_NEGSEL_APORT0XCH12                  (_ADC_SINGLECTRL_NEGSEL_APORT0XCH12 << 16) /**< Shifted mode APORT0XCH12 for ADC_SINGLECTRL */
#define ADC_SINGLECTRL_NEGSEL_APORT0XCH13                  (_ADC_SINGLECTRL_NEGSEL_APORT0XCH13 << 16) /**< Shifted mode APORT0XCH13 for ADC_SINGLECTRL */
#define ADC_SINGLECTRL_NEGSEL_APORT0XCH14                  (_ADC_SINGLECTRL_NEGSEL_APORT0XCH14 << 16) /**< Shifted mode APORT0XCH14 for ADC_SINGLECTRL */
#define ADC_SINGLECTRL_NEGSEL_APORT0XCH15                  (_ADC_SINGLECTRL_NEGSEL_APORT0XCH15 << 16) /**< Shifted mode APORT0XCH15 for ADC_SINGLECTRL */
#define ADC_SINGLECTRL_NEGSEL_APORT0YCH0                   (_ADC_SINGLECTRL_NEGSEL_APORT0YCH0 << 16)  /**< Shifted mode APORT0YCH0 for ADC_SINGLECTRL */
#define ADC_SINGLECTRL_NEGSEL_APORT0YCH1                   (_ADC_SINGLECTRL_NEGSEL_APORT0YCH1 << 16)  /**< Shifted mode APORT0YCH1 for ADC_SINGLECTRL */
#define ADC_SINGLECTRL_NEGSEL_APORT0YCH2                   (_ADC_SINGLECTRL_NEGSEL_APORT0YCH2 << 16)  /**< Shifted mode APORT0YCH2 for ADC_SINGLECTRL */
#define ADC_SINGLECTRL_NEGSEL_APORT0YCH3                   (_ADC_SINGLECTRL_NEGSEL_APORT0YCH3 << 16)  /**< Shifted mode APORT0YCH3 for ADC_SINGLECTRL */
#define ADC_SINGLECTRL_NEGSEL_APORT0YCH4                   (_ADC_SINGLECTRL_NEGSEL_APORT0YCH4 << 16)  /**< Shifted mode APORT0YCH4 for ADC_SINGLECTRL */
#define ADC_SINGLECTRL_NEGSEL_APORT0YCH5                   (_ADC_SINGLECTRL_NEGSEL_APORT0YCH5 << 16)  /**< Shifted mode APORT0YCH5 for ADC_SINGLECTRL */
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
#define ADC_SINGLECTRL_NEGSEL_APORT1XCH18                  (_ADC_SINGLECTRL_NEGSEL_APORT1XCH18 << 16) /**< Shifted mode APORT1XCH18 for ADC_SINGLECTRL */
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
