tejeez/geckokapula/gecko_sdk_suite/v2.7/platform/Device/SiliconLabs/BGM1/Include/bgm1_cmu.h

/***************************************************************************//**
 * @file
 * @brief BGM1_CMU register and bit field definitions
 *******************************************************************************
 * # License
 * <b>Copyright 2020 Silicon Laboratories Inc. www.silabs.com</b>
 *******************************************************************************
 *
 * SPDX-License-Identifier: Zlib
 *
 * The licensor of this software is Silicon Laboratories Inc.
 *
 * This software is provided 'as-is', without any express or implied
 * warranty. In no event will the authors be held liable for any damages
 * arising from the use of this software.
 *
 * Permission is granted to anyone to use this software for any purpose,
 * including commercial applications, and to alter it and redistribute it
 * freely, subject to the following restrictions:
 *
 * 1. The origin of this software must not be misrepresented; you must not
 *    claim that you wrote the original software. If you use this software
 *    in a product, an acknowledgment in the product documentation would be
 *    appreciated but is not required.
 * 2. Altered source versions must be plainly marked as such, and must not be
 *    misrepresented as being the original software.
 * 3. This notice may not be removed or altered from any source distribution.
 *
 ******************************************************************************/

#if defined(__ICCARM__)
#pragma system_include       /* Treat file as system include file. */
#elif defined(__ARMCC_VERSION) && (__ARMCC_VERSION >= 6010050)
#pragma clang system_header  /* Treat file as system include file. */
#endif

/***************************************************************************//**
 * @addtogroup Parts
 * @{
 ******************************************************************************/
/***************************************************************************//**
 * @defgroup BGM1_CMU CMU
 * @{
 * @brief BGM1_CMU Register Declaration
 ******************************************************************************/
/** CMU Register Declaration */
typedef struct {
  __IOM uint32_t CTRL;                /**< CMU Control Register  */

  uint32_t       RESERVED0[3U];       /**< Reserved for future use **/
  __IOM uint32_t HFRCOCTRL;           /**< HFRCO Control Register  */

  uint32_t       RESERVED1[1U];       /**< Reserved for future use **/
  __IOM uint32_t AUXHFRCOCTRL;        /**< AUXHFRCO Control Register  */

  uint32_t       RESERVED2[1U];       /**< Reserved for future use **/
  __IOM uint32_t LFRCOCTRL;           /**< LFRCO Control Register  */
  __IOM uint32_t HFXOCTRL;            /**< HFXO Control Register  */
  __IOM uint32_t HFXOCTRL1;           /**< HFXO Control 1  */
  __IOM uint32_t HFXOSTARTUPCTRL;     /**< HFXO Startup Control  */
  __IOM uint32_t HFXOSTEADYSTATECTRL; /**< HFXO Steady State Control  */
  __IOM uint32_t HFXOTIMEOUTCTRL;     /**< HFXO Timeout Control  */
  __IOM uint32_t LFXOCTRL;            /**< LFXO Control Register  */
  __IOM uint32_t ULFRCOCTRL;          /**< ULFRCO Control Register  */

  uint32_t       RESERVED3[4U];       /**< Reserved for future use **/
  __IOM uint32_t CALCTRL;             /**< Calibration Control Register  */
  __IOM uint32_t CALCNT;              /**< Calibration Counter Register  */
  uint32_t       RESERVED4[2U];       /**< Reserved for future use **/
  __IOM uint32_t OSCENCMD;            /**< Oscillator Enable/Disable Command Register  */
  __IOM uint32_t CMD;                 /**< Command Register  */
  uint32_t       RESERVED5[2U];       /**< Reserved for future use **/
  __IOM uint32_t DBGCLKSEL;           /**< Debug Trace Clock Select  */
  __IOM uint32_t HFCLKSEL;            /**< High Frequency Clock Select Command Register  */
  uint32_t       RESERVED6[2U];       /**< Reserved for future use **/
  __IOM uint32_t LFACLKSEL;           /**< Low Frequency A Clock Select Register  */
  __IOM uint32_t LFBCLKSEL;           /**< Low Frequency B Clock Select Register  */
  __IOM uint32_t LFECLKSEL;           /**< Low Frequency E Clock Select Register  */

  uint32_t       RESERVED7[1U];       /**< Reserved for future use **/
  __IM uint32_t  STATUS;              /**< Status Register  */
  __IM uint32_t  HFCLKSTATUS;         /**< HFCLK Status Register  */
  uint32_t       RESERVED8[1U];       /**< Reserved for future use **/
  __IM uint32_t  HFXOTRIMSTATUS;      /**< HFXO Trim Status  */
  __IM uint32_t  IF;                  /**< Interrupt Flag Register  */
  __IOM uint32_t IFS;                 /**< Interrupt Flag Set Register  */
  __IOM uint32_t IFC;                 /**< Interrupt Flag Clear Register  */
  __IOM uint32_t IEN;                 /**< Interrupt Enable Register  */
  __IOM uint32_t HFBUSCLKEN0;         /**< High Frequency Bus Clock Enable Register 0  */

  uint32_t       RESERVED9[3U];       /**< Reserved for future use **/
  __IOM uint32_t HFPERCLKEN0;         /**< High Frequency Peripheral Clock Enable Register 0  */

  uint32_t       RESERVED10[7U];      /**< Reserved for future use **/
  __IOM uint32_t LFACLKEN0;           /**< Low Frequency a Clock Enable Register 0  (Async Reg)  */
  uint32_t       RESERVED11[1U];      /**< Reserved for future use **/
  __IOM uint32_t LFBCLKEN0;           /**< Low Frequency B Clock Enable Register 0 (Async Reg)  */

  uint32_t       RESERVED12[1U];      /**< Reserved for future use **/
  __IOM uint32_t LFECLKEN0;           /**< Low Frequency E Clock Enable Register 0 (Async Reg)  */
  uint32_t       RESERVED13[3U];      /**< Reserved for future use **/
  __IOM uint32_t HFPRESC;             /**< High Frequency Clock Prescaler Register  */

  uint32_t       RESERVED14[1U];      /**< Reserved for future use **/
  __IOM uint32_t HFCOREPRESC;         /**< High Frequency Core Clock Prescaler Register  */
  __IOM uint32_t HFPERPRESC;          /**< High Frequency Peripheral Clock Prescaler Register  */

  uint32_t       RESERVED15[1U];      /**< Reserved for future use **/
  __IOM uint32_t HFEXPPRESC;          /**< High Frequency Export Clock Prescaler Register  */

  uint32_t       RESERVED16[2U];      /**< Reserved for future use **/
  __IOM uint32_t LFAPRESC0;           /**< Low Frequency a Prescaler Register 0 (Async Reg)  */
  uint32_t       RESERVED17[1U];      /**< Reserved for future use **/
  __IOM uint32_t LFBPRESC0;           /**< Low Frequency B Prescaler Register 0  (Async Reg)  */
  uint32_t       RESERVED18[1U];      /**< Reserved for future use **/
  __IOM uint32_t LFEPRESC0;           /**< Low Frequency E Prescaler Register 0  (Async Reg)  */

  uint32_t       RESERVED19[3U];      /**< Reserved for future use **/
  __IM uint32_t  SYNCBUSY;            /**< Synchronization Busy Register  */
  __IOM uint32_t FREEZE;              /**< Freeze Register  */
  uint32_t       RESERVED20[2U];      /**< Reserved for future use **/
  __IOM uint32_t PCNTCTRL;            /**< PCNT Control Register  */

  uint32_t       RESERVED21[2U];      /**< Reserved for future use **/
  __IOM uint32_t ADCCTRL;             /**< ADC Control Register  */

  uint32_t       RESERVED22[4U];      /**< Reserved for future use **/
  __IOM uint32_t ROUTEPEN;            /**< I/O Routing Pin Enable Register  */
  __IOM uint32_t ROUTELOC0;           /**< I/O Routing Location Register  */

  uint32_t       RESERVED23[2U];      /**< Reserved for future use **/
  __IOM uint32_t LOCK;                /**< Configuration Lock Register  */
} CMU_TypeDef;                        /** @} */

/***************************************************************************//**
 * @addtogroup BGM1_CMU
 * @{
 * @defgroup BGM1_CMU_BitFields  CMU Bit Fields
 * @{
 ******************************************************************************/

/* Bit fields for CMU CTRL */
#define _CMU_CTRL_RESETVALUE                              0x00300000UL                          /**< Default value for CMU_CTRL */
#define _CMU_CTRL_MASK                                    0x001101EFUL                          /**< Mask for CMU_CTRL */
#define _CMU_CTRL_CLKOUTSEL0_SHIFT                        0                                     /**< Shift value for CMU_CLKOUTSEL0 */
#define _CMU_CTRL_CLKOUTSEL0_MASK                         0xFUL                                 /**< Bit mask for CMU_CLKOUTSEL0 */
#define _CMU_CTRL_CLKOUTSEL0_DEFAULT                      0x00000000UL                          /**< Mode DEFAULT for CMU_CTRL */
#define _CMU_CTRL_CLKOUTSEL0_DISABLED                     0x00000000UL                          /**< Mode DISABLED for CMU_CTRL */
#define _CMU_CTRL_CLKOUTSEL0_ULFRCO                       0x00000001UL                          /**< Mode ULFRCO for CMU_CTRL */
#define _CMU_CTRL_CLKOUTSEL0_LFRCO                        0x00000002UL                          /**< Mode LFRCO for CMU_CTRL */
#define _CMU_CTRL_CLKOUTSEL0_LFXO                         0x00000003UL                          /**< Mode LFXO for CMU_CTRL */
#define _CMU_CTRL_CLKOUTSEL0_HFXO                         0x00000006UL                          /**< Mode HFXO for CMU_CTRL */
#define _CMU_CTRL_CLKOUTSEL0_HFEXPCLK                     0x00000007UL                          /**< Mode HFEXPCLK for CMU_CTRL */
#define _CMU_CTRL_CLKOUTSEL0_ULFRCOQ                      0x00000009UL                          /**< Mode ULFRCOQ for CMU_CTRL */
#define _CMU_CTRL_CLKOUTSEL0_LFRCOQ                       0x0000000AUL                          /**< Mode LFRCOQ for CMU_CTRL */
#define _CMU_CTRL_CLKOUTSEL0_LFXOQ                        0x0000000BUL                          /**< Mode LFXOQ for CMU_CTRL */
#define _CMU_CTRL_CLKOUTSEL0_HFRCOQ                       0x0000000CUL                          /**< Mode HFRCOQ for CMU_CTRL */
#define _CMU_CTRL_CLKOUTSEL0_AUXHFRCOQ                    0x0000000DUL                          /**< Mode AUXHFRCOQ for CMU_CTRL */
#define _CMU_CTRL_CLKOUTSEL0_HFXOQ                        0x0000000EUL                          /**< Mode HFXOQ for CMU_CTRL */
#define _CMU_CTRL_CLKOUTSEL0_HFSRCCLK                     0x0000000FUL                          /**< Mode HFSRCCLK for CMU_CTRL */
#define CMU_CTRL_CLKOUTSEL0_DEFAULT                       (_CMU_CTRL_CLKOUTSEL0_DEFAULT << 0)   /**< Shifted mode DEFAULT for CMU_CTRL */
#define CMU_CTRL_CLKOUTSEL0_DISABLED                      (_CMU_CTRL_CLKOUTSEL0_DISABLED << 0)  /**< Shifted mode DISABLED for CMU_CTRL */
#define CMU_CTRL_CLKOUTSEL0_ULFRCO                        (_CMU_CTRL_CLKOUTSEL0_ULFRCO << 0)    /**< Shifted mode ULFRCO for CMU_CTRL */
#define CMU_CTRL_CLKOUTSEL0_LFRCO                         (_CMU_CTRL_CLKOUTSEL0_LFRCO << 0)     /**< Shifted mode LFRCO for CMU_CTRL */
#define CMU_CTRL_CLKOUTSEL0_LFXO                          (_CMU_CTRL_CLKOUTSEL0_LFXO << 0)      /**< Shifted mode LFXO for CMU_CTRL */
#define CMU_CTRL_CLKOUTSEL0_HFXO                          (_CMU_CTRL_CLKOUTSEL0_HFXO << 0)      /**< Shifted mode HFXO for CMU_CTRL */
#define CMU_CTRL_CLKOUTSEL0_HFEXPCLK                      (_CMU_CTRL_CLKOUTSEL0_HFEXPCLK << 0)  /**< Shifted mode HFEXPCLK for CMU_CTRL */
#define CMU_CTRL_CLKOUTSEL0_ULFRCOQ                       (_CMU_CTRL_CLKOUTSEL0_ULFRCOQ << 0)   /**< Shifted mode ULFRCOQ for CMU_CTRL */
#define CMU_CTRL_CLKOUTSEL0_LFRCOQ                        (_CMU_CTRL_CLKOUTSEL0_LFRCOQ << 0)    /**< Shifted mode LFRCOQ for CMU_CTRL */
#define CMU_CTRL_CLKOUTSEL0_LFXOQ                         (_CMU_CTRL_CLKOUTSEL0_LFXOQ << 0)     /**< Shifted mode LFXOQ for CMU_CTRL */
#define CMU_CTRL_CLKOUTSEL0_HFRCOQ                        (_CMU_CTRL_CLKOUTSEL0_HFRCOQ << 0)    /**< Shifted mode HFRCOQ for CMU_CTRL */
#define CMU_CTRL_CLKOUTSEL0_AUXHFRCOQ                     (_CMU_CTRL_CLKOUTSEL0_AUXHFRCOQ << 0) /**< Shifted mode AUXHFRCOQ for CMU_CTRL */
#define CMU_CTRL_CLKOUTSEL0_HFXOQ                         (_CMU_CTRL_CLKOUTSEL0_HFXOQ << 0)     /**< Shifted mode HFXOQ for CMU_CTRL */
#define CMU_CTRL_CLKOUTSEL0_HFSRCCLK                      (_CMU_CTRL_CLKOUTSEL0_HFSRCCLK << 0)  /**< Shifted mode HFSRCCLK for CMU_CTRL */
#define _CMU_CTRL_CLKOUTSEL1_SHIFT                        5                                     /**< Shift value for CMU_CLKOUTSEL1 */
#define _CMU_CTRL_CLKOUTSEL1_MASK                         0x1E0UL                               /**< Bit mask for CMU_CLKOUTSEL1 */
#define _CMU_CTRL_CLKOUTSEL1_DEFAULT                      0x00000000UL                          /**< Mode DEFAULT for CMU_CTRL */
#define _CMU_CTRL_CLKOUTSEL1_DISABLED                     0x00000000UL                          /**< Mode DISABLED for CMU_CTRL */
#define _CMU_CTRL_CLKOUTSEL1_ULFRCO                       0x00000001UL                          /**< Mode ULFRCO for CMU_CTRL */
#define _CMU_CTRL_CLKOUTSEL1_LFRCO                        0x00000002UL                          /**< Mode LFRCO for CMU_CTRL */
#define _CMU_CTRL_CLKOUTSEL1_LFXO                         0x00000003UL                          /**< Mode LFXO for CMU_CTRL */
#define _CMU_CTRL_CLKOUTSEL1_HFXO                         0x00000006UL                          /**< Mode HFXO for CMU_CTRL */
#define _CMU_CTRL_CLKOUTSEL1_HFEXPCLK                     0x00000007UL                          /**< Mode HFEXPCLK for CMU_CTRL */
#define _CMU_CTRL_CLKOUTSEL1_ULFRCOQ                      0x00000009UL                          /**< Mode ULFRCOQ for CMU_CTRL */
#define _CMU_CTRL_CLKOUTSEL1_LFRCOQ                       0x0000000AUL                          /**< Mode LFRCOQ for CMU_CTRL */
#define _CMU_CTRL_CLKOUTSEL1_LFXOQ                        0x0000000BUL                          /**< Mode LFXOQ for CMU_CTRL */
#define _CMU_CTRL_CLKOUTSEL1_HFRCOQ                       0x0000000CUL                          /**< Mode HFRCOQ for CMU_CTRL */
#define _CMU_CTRL_CLKOUTSEL1_AUXHFRCOQ                    0x0000000DUL                          /**< Mode AUXHFRCOQ for CMU_CTRL */
#define _CMU_CTRL_CLKOUTSEL1_HFXOQ                        0x0000000EUL                          /**< Mode HFXOQ for CMU_CTRL */
#define _CMU_CTRL_CLKOUTSEL1_HFSRCCLK                     0x0000000FUL                          /**< Mode HFSRCCLK for CMU_CTRL */
#define CMU_CTRL_CLKOUTSEL1_DEFAULT                       (_CMU_CTRL_CLKOUTSEL1_DEFAULT << 5)   /**< Shifted mode DEFAULT for CMU_CTRL */
#define CMU_CTRL_CLKOUTSEL1_DISABLED                      (_CMU_CTRL_CLKOUTSEL1_DISABLED << 5)  /**< Shifted mode DISABLED for CMU_CTRL */
#define CMU_CTRL_CLKOUTSEL1_ULFRCO                        (_CMU_CTRL_CLKOUTSEL1_ULFRCO << 5)    /**< Shifted mode ULFRCO for CMU_CTRL */
#define CMU_CTRL_CLKOUTSEL1_LFRCO                         (_CMU_CTRL_CLKOUTSEL1_LFRCO << 5)     /**< Shifted mode LFRCO for CMU_CTRL */
#define CMU_CTRL_CLKOUTSEL1_LFXO                          (_CMU_CTRL_CLKOUTSEL1_LFXO << 5)      /**< Shifted mode LFXO for CMU_CTRL */
#define CMU_CTRL_CLKOUTSEL1_HFXO                          (_CMU_CTRL_CLKOUTSEL1_HFXO << 5)      /**< Shifted mode HFXO for CMU_CTRL */
#define CMU_CTRL_CLKOUTSEL1_HFEXPCLK                      (_CMU_CTRL_CLKOUTSEL1_HFEXPCLK << 5)  /**< Shifted mode HFEXPCLK for CMU_CTRL */
#define CMU_CTRL_CLKOUTSEL1_ULFRCOQ                       (_CMU_CTRL_CLKOUTSEL1_ULFRCOQ << 5)   /**< Shifted mode ULFRCOQ for CMU_CTRL */
#define CMU_CTRL_CLKOUTSEL1_LFRCOQ                        (_CMU_CTRL_CLKOUTSEL1_LFRCOQ << 5)    /**< Shifted mode LFRCOQ for CMU_CTRL */
#define CMU_CTRL_CLKOUTSEL1_LFXOQ                         (_CMU_CTRL_CLKOUTSEL1_LFXOQ << 5)     /**< Shifted mode LFXOQ for CMU_CTRL */
#define CMU_CTRL_CLKOUTSEL1_HFRCOQ                        (_CMU_CTRL_CLKOUTSEL1_HFRCOQ << 5)    /**< Shifted mode HFRCOQ for CMU_CTRL */
#define CMU_CTRL_CLKOUTSEL1_AUXHFRCOQ                     (_CMU_CTRL_CLKOUTSEL1_AUXHFRCOQ << 5) /**< Shifted mode AUXHFRCOQ for CMU_CTRL */
#define CMU_CTRL_CLKOUTSEL1_HFXOQ                         (_CMU_CTRL_CLKOUTSEL1_HFXOQ << 5)     /**< Shifted mode HFXOQ for CMU_CTRL */
#define CMU_CTRL_CLKOUTSEL1_HFSRCCLK                      (_CMU_CTRL_CLKOUTSEL1_HFSRCCLK << 5)  /**< Shifted mode HFSRCCLK for CMU_CTRL */
#define CMU_CTRL_WSHFLE                                   (0x1UL << 16)                         /**< Wait State for High-Frequency LE Interface */
#define _CMU_CTRL_WSHFLE_SHIFT                            16                                    /**< Shift value for CMU_WSHFLE */
#define _CMU_CTRL_WSHFLE_MASK                             0x10000UL                             /**< Bit mask for CMU_WSHFLE */
#define _CMU_CTRL_WSHFLE_DEFAULT                          0x00000000UL                          /**< Mode DEFAULT for CMU_CTRL */
#define CMU_CTRL_WSHFLE_DEFAULT                           (_CMU_CTRL_WSHFLE_DEFAULT << 16)      /**< Shifted mode DEFAULT for CMU_CTRL */
#define CMU_CTRL_HFPERCLKEN                               (0x1UL << 20)                         /**< HFPERCLK Enable */
#define _CMU_CTRL_HFPERCLKEN_SHIFT                        20                                    /**< Shift value for CMU_HFPERCLKEN */
#define _CMU_CTRL_HFPERCLKEN_MASK                         0x100000UL                            /**< Bit mask for CMU_HFPERCLKEN */
#define _CMU_CTRL_HFPERCLKEN_DEFAULT                      0x00000001UL                          /**< Mode DEFAULT for CMU_CTRL */
#define CMU_CTRL_HFPERCLKEN_DEFAULT                       (_CMU_CTRL_HFPERCLKEN_DEFAULT << 20)  /**< Shifted mode DEFAULT for CMU_CTRL */

/* Bit fields for CMU HFRCOCTRL */
#define _CMU_HFRCOCTRL_RESETVALUE                         0xB1481F3CUL                                /**< Default value for CMU_HFRCOCTRL */
#define _CMU_HFRCOCTRL_MASK                               0xFFFF3F7FUL                                /**< Mask for CMU_HFRCOCTRL */
#define _CMU_HFRCOCTRL_TUNING_SHIFT                       0                                           /**< Shift value for CMU_TUNING */
#define _CMU_HFRCOCTRL_TUNING_MASK                        0x7FUL                                      /**< Bit mask for CMU_TUNING */
#define _CMU_HFRCOCTRL_TUNING_DEFAULT                     0x0000003CUL                                /**< Mode DEFAULT for CMU_HFRCOCTRL */
#define CMU_HFRCOCTRL_TUNING_DEFAULT                      (_CMU_HFRCOCTRL_TUNING_DEFAULT << 0)        /**< Shifted mode DEFAULT for CMU_HFRCOCTRL */
#define _CMU_HFRCOCTRL_FINETUNING_SHIFT                   8                                           /**< Shift value for CMU_FINETUNING */
#define _CMU_HFRCOCTRL_FINETUNING_MASK                    0x3F00UL                                    /**< Bit mask for CMU_FINETUNING */
#define _CMU_HFRCOCTRL_FINETUNING_DEFAULT                 0x0000001FUL                                /**< Mode DEFAULT for CMU_HFRCOCTRL */
#define CMU_HFRCOCTRL_FINETUNING_DEFAULT                  (_CMU_HFRCOCTRL_FINETUNING_DEFAULT << 8)    /**< Shifted mode DEFAULT for CMU_HFRCOCTRL */
#define _CMU_HFRCOCTRL_FREQRANGE_SHIFT                    16                                          /**< Shift value for CMU_FREQRANGE */
#define _CMU_HFRCOCTRL_FREQRANGE_MASK                     0x1F0000UL                                  /**< Bit mask for CMU_FREQRANGE */
#define _CMU_HFRCOCTRL_FREQRANGE_DEFAULT                  0x00000008UL                                /**< Mode DEFAULT for CMU_HFRCOCTRL */
#define CMU_HFRCOCTRL_FREQRANGE_DEFAULT                   (_CMU_HFRCOCTRL_FREQRANGE_DEFAULT << 16)    /**< Shifted mode DEFAULT for CMU_HFRCOCTRL */
#define _CMU_HFRCOCTRL_CMPBIAS_SHIFT                      21                                          /**< Shift value for CMU_CMPBIAS */
#define _CMU_HFRCOCTRL_CMPBIAS_MASK                       0xE00000UL                                  /**< Bit mask for CMU_CMPBIAS */
#define _CMU_HFRCOCTRL_CMPBIAS_DEFAULT                    0x00000002UL                                /**< Mode DEFAULT for CMU_HFRCOCTRL */
#define CMU_HFRCOCTRL_CMPBIAS_DEFAULT                     (_CMU_HFRCOCTRL_CMPBIAS_DEFAULT << 21)      /**< Shifted mode DEFAULT for CMU_HFRCOCTRL */
#define CMU_HFRCOCTRL_LDOHP                               (0x1UL << 24)                               /**< HFRCO LDO High Power Mode */
#define _CMU_HFRCOCTRL_LDOHP_SHIFT                        24                                          /**< Shift value for CMU_LDOHP */
#define _CMU_HFRCOCTRL_LDOHP_MASK                         0x1000000UL                                 /**< Bit mask for CMU_LDOHP */
#define _CMU_HFRCOCTRL_LDOHP_DEFAULT                      0x00000001UL                                /**< Mode DEFAULT for CMU_HFRCOCTRL */
#define CMU_HFRCOCTRL_LDOHP_DEFAULT                       (_CMU_HFRCOCTRL_LDOHP_DEFAULT << 24)        /**< Shifted mode DEFAULT for CMU_HFRCOCTRL */
#define _CMU_HFRCOCTRL_CLKDIV_SHIFT                       25                                          /**< Shift value for CMU_CLKDIV */
#define _CMU_HFRCOCTRL_CLKDIV_MASK                        0x6000000UL                                 /**< Bit mask for CMU_CLKDIV */
#define _CMU_HFRCOCTRL_CLKDIV_DEFAULT                     0x00000000UL                                /**< Mode DEFAULT for CMU_HFRCOCTRL */
#define _CMU_HFRCOCTRL_CLKDIV_DIV1                        0x00000000UL                                /**< Mode DIV1 for CMU_HFRCOCTRL */
#define _CMU_HFRCOCTRL_CLKDIV_DIV2                        0x00000001UL                                /**< Mode DIV2 for CMU_HFRCOCTRL */
#define _CMU_HFRCOCTRL_CLKDIV_DIV4                        0x00000002UL                                /**< Mode DIV4 for CMU_HFRCOCTRL */
#define CMU_HFRCOCTRL_CLKDIV_DEFAULT                      (_CMU_HFRCOCTRL_CLKDIV_DEFAULT << 25)       /**< Shifted mode DEFAULT for CMU_HFRCOCTRL */
#define CMU_HFRCOCTRL_CLKDIV_DIV1                         (_CMU_HFRCOCTRL_CLKDIV_DIV1 << 25)          /**< Shifted mode DIV1 for CMU_HFRCOCTRL */
#define CMU_HFRCOCTRL_CLKDIV_DIV2                         (_CMU_HFRCOCTRL_CLKDIV_DIV2 << 25)          /**< Shifted mode DIV2 for CMU_HFRCOCTRL */
#define CMU_HFRCOCTRL_CLKDIV_DIV4                         (_CMU_HFRCOCTRL_CLKDIV_DIV4 << 25)          /**< Shifted mode DIV4 for CMU_HFRCOCTRL */
#define CMU_HFRCOCTRL_FINETUNINGEN                        (0x1UL << 27)                               /**< Enable Reference for Fine Tuning */
#define _CMU_HFRCOCTRL_FINETUNINGEN_SHIFT                 27                                          /**< Shift value for CMU_FINETUNINGEN */
#define _CMU_HFRCOCTRL_FINETUNINGEN_MASK                  0x8000000UL                                 /**< Bit mask for CMU_FINETUNINGEN */
#define _CMU_HFRCOCTRL_FINETUNINGEN_DEFAULT               0x00000000UL                                /**< Mode DEFAULT for CMU_HFRCOCTRL */
#define CMU_HFRCOCTRL_FINETUNINGEN_DEFAULT                (_CMU_HFRCOCTRL_FINETUNINGEN_DEFAULT << 27) /**< Shifted mode DEFAULT for CMU_HFRCOCTRL */
#define _CMU_HFRCOCTRL_VREFTC_SHIFT                       28                                          /**< Shift value for CMU_VREFTC */
#define _CMU_HFRCOCTRL_VREFTC_MASK                        0xF0000000UL                                /**< Bit mask for CMU_VREFTC */
#define _CMU_HFRCOCTRL_VREFTC_DEFAULT                     0x0000000BUL                                /**< Mode DEFAULT for CMU_HFRCOCTRL */
#define CMU_HFRCOCTRL_VREFTC_DEFAULT                      (_CMU_HFRCOCTRL_VREFTC_DEFAULT << 28)       /**< Shifted mode DEFAULT for CMU_HFRCOCTRL */

/* Bit fields for CMU AUXHFRCOCTRL */
#define _CMU_AUXHFRCOCTRL_RESETVALUE                      0xB1481F3CUL                                   /**< Default value for CMU_AUXHFRCOCTRL */
#define _CMU_AUXHFRCOCTRL_MASK                            0xFFFF3F7FUL                                   /**< Mask for CMU_AUXHFRCOCTRL */
#define _CMU_AUXHFRCOCTRL_TUNING_SHIFT                    0                                              /**< Shift value for CMU_TUNING */
#define _CMU_AUXHFRCOCTRL_TUNING_MASK                     0x7FUL                                         /**< Bit mask for CMU_TUNING */
#define _CMU_AUXHFRCOCTRL_TUNING_DEFAULT                  0x0000003CUL                                   /**< Mode DEFAULT for CMU_AUXHFRCOCTRL */
#define CMU_AUXHFRCOCTRL_TUNING_DEFAULT                   (_CMU_AUXHFRCOCTRL_TUNING_DEFAULT << 0)        /**< Shifted mode DEFAULT for CMU_AUXHFRCOCTRL */
#define _CMU_AUXHFRCOCTRL_FINETUNING_SHIFT                8                                              /**< Shift value for CMU_FINETUNING */
#define _CMU_AUXHFRCOCTRL_FINETUNING_MASK                 0x3F00UL                                       /**< Bit mask for CMU_FINETUNING */
#define _CMU_AUXHFRCOCTRL_FINETUNING_DEFAULT              0x0000001FUL                                   /**< Mode DEFAULT for CMU_AUXHFRCOCTRL */
#define CMU_AUXHFRCOCTRL_FINETUNING_DEFAULT               (_CMU_AUXHFRCOCTRL_FINETUNING_DEFAULT << 8)    /**< Shifted mode DEFAULT for CMU_AUXHFRCOCTRL */
#define _CMU_AUXHFRCOCTRL_FREQRANGE_SHIFT                 16                                             /**< Shift value for CMU_FREQRANGE */
#define _CMU_AUXHFRCOCTRL_FREQRANGE_MASK                  0x1F0000UL                                     /**< Bit mask for CMU_FREQRANGE */
#define _CMU_AUXHFRCOCTRL_FREQRANGE_DEFAULT               0x00000008UL                                   /**< Mode DEFAULT for CMU_AUXHFRCOCTRL */
#define CMU_AUXHFRCOCTRL_FREQRANGE_DEFAULT                (_CMU_AUXHFRCOCTRL_FREQRANGE_DEFAULT << 16)    /**< Shifted mode DEFAULT for CMU_AUXHFRCOCTRL */
#define _CMU_AUXHFRCOCTRL_CMPBIAS_SHIFT                   21                                             /**< Shift value for CMU_CMPBIAS */
#define _CMU_AUXHFRCOCTRL_CMPBIAS_MASK                    0xE00000UL                                     /**< Bit mask for CMU_CMPBIAS */
#define _CMU_AUXHFRCOCTRL_CMPBIAS_DEFAULT                 0x00000002UL                                   /**< Mode DEFAULT for CMU_AUXHFRCOCTRL */
#define CMU_AUXHFRCOCTRL_CMPBIAS_DEFAULT                  (_CMU_AUXHFRCOCTRL_CMPBIAS_DEFAULT << 21)      /**< Shifted mode DEFAULT for CMU_AUXHFRCOCTRL */
#define CMU_AUXHFRCOCTRL_LDOHP                            (0x1UL << 24)                                  /**< AUXHFRCO LDO High Power Mode */
#define _CMU_AUXHFRCOCTRL_LDOHP_SHIFT                     24                                             /**< Shift value for CMU_LDOHP */
#define _CMU_AUXHFRCOCTRL_LDOHP_MASK                      0x1000000UL                                    /**< Bit mask for CMU_LDOHP */
#define _CMU_AUXHFRCOCTRL_LDOHP_DEFAULT                   0x00000001UL                                   /**< Mode DEFAULT for CMU_AUXHFRCOCTRL */
#define CMU_AUXHFRCOCTRL_LDOHP_DEFAULT                    (_CMU_AUXHFRCOCTRL_LDOHP_DEFAULT << 24)        /**< Shifted mode DEFAULT for CMU_AUXHFRCOCTRL */
#define _CMU_AUXHFRCOCTRL_CLKDIV_SHIFT                    25                                             /**< Shift value for CMU_CLKDIV */
#define _CMU_AUXHFRCOCTRL_CLKDIV_MASK                     0x6000000UL                                    /**< Bit mask for CMU_CLKDIV */
#define _CMU_AUXHFRCOCTRL_CLKDIV_DEFAULT                  0x00000000UL                                   /**< Mode DEFAULT for CMU_AUXHFRCOCTRL */
#define _CMU_AUXHFRCOCTRL_CLKDIV_DIV1                     0x00000000UL                                   /**< Mode DIV1 for CMU_AUXHFRCOCTRL */
#define _CMU_AUXHFRCOCTRL_CLKDIV_DIV2                     0x00000001UL                                   /**< Mode DIV2 for CMU_AUXHFRCOCTRL */
#define _CMU_AUXHFRCOCTRL_CLKDIV_DIV4                     0x00000002UL                                   /**< Mode DIV4 for CMU_AUXHFRCOCTRL */
#define CMU_AUXHFRCOCTRL_CLKDIV_DEFAULT                   (_CMU_AUXHFRCOCTRL_CLKDIV_DEFAULT << 25)       /**< Shifted mode DEFAULT for CMU_AUXHFRCOCTRL */
#define CMU_AUXHFRCOCTRL_CLKDIV_DIV1                      (_CMU_AUXHFRCOCTRL_CLKDIV_DIV1 << 25)          /**< Shifted mode DIV1 for CMU_AUXHFRCOCTRL */
#define CMU_AUXHFRCOCTRL_CLKDIV_DIV2                      (_CMU_AUXHFRCOCTRL_CLKDIV_DIV2 << 25)          /**< Shifted mode DIV2 for CMU_AUXHFRCOCTRL */
#define CMU_AUXHFRCOCTRL_CLKDIV_DIV4                      (_CMU_AUXHFRCOCTRL_CLKDIV_DIV4 << 25)          /**< Shifted mode DIV4 for CMU_AUXHFRCOCTRL */
#define CMU_AUXHFRCOCTRL_FINETUNINGEN                     (0x1UL << 27)                                  /**< Enable Reference for Fine Tuning */
#define _CMU_AUXHFRCOCTRL_FINETUNINGEN_SHIFT              27                                             /**< Shift value for CMU_FINETUNINGEN */
#define _CMU_AUXHFRCOCTRL_FINETUNINGEN_MASK               0x8000000UL                                    /**< Bit mask for CMU_FINETUNINGEN */
#define _CMU_AUXHFRCOCTRL_FINETUNINGEN_DEFAULT            0x00000000UL                                   /**< Mode DEFAULT for CMU_AUXHFRCOCTRL */
#define CMU_AUXHFRCOCTRL_FINETUNINGEN_DEFAULT             (_CMU_AUXHFRCOCTRL_FINETUNINGEN_DEFAULT << 27) /**< Shifted mode DEFAULT for CMU_AUXHFRCOCTRL */
#define _CMU_AUXHFRCOCTRL_VREFTC_SHIFT                    28                                             /**< Shift value for CMU_VREFTC */
#define _CMU_AUXHFRCOCTRL_VREFTC_MASK                     0xF0000000UL                                   /**< Bit mask for CMU_VREFTC */
#define _CMU_AUXHFRCOCTRL_VREFTC_DEFAULT                  0x0000000BUL                                   /**< Mode DEFAULT for CMU_AUXHFRCOCTRL */
#define CMU_AUXHFRCOCTRL_VREFTC_DEFAULT                   (_CMU_AUXHFRCOCTRL_VREFTC_DEFAULT << 28)       /**< Shifted mode DEFAULT for CMU_AUXHFRCOCTRL */

/* Bit fields for CMU LFRCOCTRL */
#define _CMU_LFRCOCTRL_RESETVALUE                         0x81060100UL                              /**< Default value for CMU_LFRCOCTRL */
#define _CMU_LFRCOCTRL_MASK                               0xF30701FFUL                              /**< Mask for CMU_LFRCOCTRL */
#define _CMU_LFRCOCTRL_TUNING_SHIFT                       0                                         /**< Shift value for CMU_TUNING */
#define _CMU_LFRCOCTRL_TUNING_MASK                        0x1FFUL                                   /**< Bit mask for CMU_TUNING */
#define _CMU_LFRCOCTRL_TUNING_DEFAULT                     0x00000100UL                              /**< Mode DEFAULT for CMU_LFRCOCTRL */
#define CMU_LFRCOCTRL_TUNING_DEFAULT                      (_CMU_LFRCOCTRL_TUNING_DEFAULT << 0)      /**< Shifted mode DEFAULT for CMU_LFRCOCTRL */
#define CMU_LFRCOCTRL_ENVREF                              (0x1UL << 16)                             /**< Enable Duty Cycling of Vref */
#define _CMU_LFRCOCTRL_ENVREF_SHIFT                       16                                        /**< Shift value for CMU_ENVREF */
#define _CMU_LFRCOCTRL_ENVREF_MASK                        0x10000UL                                 /**< Bit mask for CMU_ENVREF */
#define _CMU_LFRCOCTRL_ENVREF_DEFAULT                     0x00000000UL                              /**< Mode DEFAULT for CMU_LFRCOCTRL */
#define CMU_LFRCOCTRL_ENVREF_DEFAULT                      (_CMU_LFRCOCTRL_ENVREF_DEFAULT << 16)     /**< Shifted mode DEFAULT for CMU_LFRCOCTRL */
#define CMU_LFRCOCTRL_ENCHOP                              (0x1UL << 17)                             /**< Enable Comparator Chopping */
#define _CMU_LFRCOCTRL_ENCHOP_SHIFT                       17                                        /**< Shift value for CMU_ENCHOP */
#define _CMU_LFRCOCTRL_ENCHOP_MASK                        0x20000UL                                 /**< Bit mask for CMU_ENCHOP */
#define _CMU_LFRCOCTRL_ENCHOP_DEFAULT                     0x00000001UL                              /**< Mode DEFAULT for CMU_LFRCOCTRL */
#define CMU_LFRCOCTRL_ENCHOP_DEFAULT                      (_CMU_LFRCOCTRL_ENCHOP_DEFAULT << 17)     /**< Shifted mode DEFAULT for CMU_LFRCOCTRL */
#define CMU_LFRCOCTRL_ENDEM                               (0x1UL << 18)                             /**< Enable Dynamic Element Matching */
#define _CMU_LFRCOCTRL_ENDEM_SHIFT                        18                                        /**< Shift value for CMU_ENDEM */
#define _CMU_LFRCOCTRL_ENDEM_MASK                         0x40000UL                                 /**< Bit mask for CMU_ENDEM */
#define _CMU_LFRCOCTRL_ENDEM_DEFAULT                      0x00000001UL                              /**< Mode DEFAULT for CMU_LFRCOCTRL */
#define CMU_LFRCOCTRL_ENDEM_DEFAULT                       (_CMU_LFRCOCTRL_ENDEM_DEFAULT << 18)      /**< Shifted mode DEFAULT for CMU_LFRCOCTRL */
#define _CMU_LFRCOCTRL_TIMEOUT_SHIFT                      24                                        /**< Shift value for CMU_TIMEOUT */
#define _CMU_LFRCOCTRL_TIMEOUT_MASK                       0x3000000UL                               /**< Bit mask for CMU_TIMEOUT */
#define _CMU_LFRCOCTRL_TIMEOUT_2CYCLES                    0x00000000UL                              /**< Mode 2CYCLES for CMU_LFRCOCTRL */
#define _CMU_LFRCOCTRL_TIMEOUT_DEFAULT                    0x00000001UL                              /**< Mode DEFAULT for CMU_LFRCOCTRL */
#define _CMU_LFRCOCTRL_TIMEOUT_16CYCLES                   0x00000001UL                              /**< Mode 16CYCLES for CMU_LFRCOCTRL */
#define _CMU_LFRCOCTRL_TIMEOUT_32CYCLES                   0x00000002UL                              /**< Mode 32CYCLES for CMU_LFRCOCTRL */
#define CMU_LFRCOCTRL_TIMEOUT_2CYCLES                     (_CMU_LFRCOCTRL_TIMEOUT_2CYCLES << 24)    /**< Shifted mode 2CYCLES for CMU_LFRCOCTRL */
#define CMU_LFRCOCTRL_TIMEOUT_DEFAULT                     (_CMU_LFRCOCTRL_TIMEOUT_DEFAULT << 24)    /**< Shifted mode DEFAULT for CMU_LFRCOCTRL */
#define CMU_LFRCOCTRL_TIMEOUT_16CYCLES                    (_CMU_LFRCOCTRL_TIMEOUT_16CYCLES << 24)   /**< Shifted mode 16CYCLES for CMU_LFRCOCTRL */
#define CMU_LFRCOCTRL_TIMEOUT_32CYCLES                    (_CMU_LFRCOCTRL_TIMEOUT_32CYCLES << 24)   /**< Shifted mode 32CYCLES for CMU_LFRCOCTRL */
#define _CMU_LFRCOCTRL_GMCCURTUNE_SHIFT                   28                                        /**< Shift value for CMU_GMCCURTUNE */
#define _CMU_LFRCOCTRL_GMCCURTUNE_MASK                    0xF0000000UL                              /**< Bit mask for CMU_GMCCURTUNE */
#define _CMU_LFRCOCTRL_GMCCURTUNE_DEFAULT                 0x00000008UL                              /**< Mode DEFAULT for CMU_LFRCOCTRL */
#define CMU_LFRCOCTRL_GMCCURTUNE_DEFAULT                  (_CMU_LFRCOCTRL_GMCCURTUNE_DEFAULT << 28) /**< Shifted mode DEFAULT for CMU_LFRCOCTRL */

/* Bit fields for CMU HFXOCTRL */
#define _CMU_HFXOCTRL_RESETVALUE                          0x00000000UL                                     /**< Default value for CMU_HFXOCTRL */
#define _CMU_HFXOCTRL_MASK                                0x37000731UL                                     /**< Mask for CMU_HFXOCTRL */
#define CMU_HFXOCTRL_MODE                                 (0x1UL << 0)                                     /**< HFXO Mode */
#define _CMU_HFXOCTRL_MODE_SHIFT                          0                                                /**< Shift value for CMU_MODE */
#define _CMU_HFXOCTRL_MODE_MASK                           0x1UL                                            /**< Bit mask for CMU_MODE */
#define _CMU_HFXOCTRL_MODE_DEFAULT                        0x00000000UL                                     /**< Mode DEFAULT for CMU_HFXOCTRL */
#define _CMU_HFXOCTRL_MODE_XTAL                           0x00000000UL                                     /**< Mode XTAL for CMU_HFXOCTRL */
#define _CMU_HFXOCTRL_MODE_EXTCLK                         0x00000001UL                                     /**< Mode EXTCLK for CMU_HFXOCTRL */
#define CMU_HFXOCTRL_MODE_DEFAULT                         (_CMU_HFXOCTRL_MODE_DEFAULT << 0)                /**< Shifted mode DEFAULT for CMU_HFXOCTRL */
#define CMU_HFXOCTRL_MODE_XTAL                            (_CMU_HFXOCTRL_MODE_XTAL << 0)                   /**< Shifted mode XTAL for CMU_HFXOCTRL */
#define CMU_HFXOCTRL_MODE_EXTCLK                          (_CMU_HFXOCTRL_MODE_EXTCLK << 0)                 /**< Shifted mode EXTCLK for CMU_HFXOCTRL */
#define _CMU_HFXOCTRL_PEAKDETSHUNTOPTMODE_SHIFT           4                                                /**< Shift value for CMU_PEAKDETSHUNTOPTMODE */
#define _CMU_HFXOCTRL_PEAKDETSHUNTOPTMODE_MASK            0x30UL                                           /**< Bit mask for CMU_PEAKDETSHUNTOPTMODE */
#define _CMU_HFXOCTRL_PEAKDETSHUNTOPTMODE_DEFAULT         0x00000000UL                                     /**< Mode DEFAULT for CMU_HFXOCTRL */
#define _CMU_HFXOCTRL_PEAKDETSHUNTOPTMODE_AUTOCMD         0x00000000UL                                     /**< Mode AUTOCMD for CMU_HFXOCTRL */
#define _CMU_HFXOCTRL_PEAKDETSHUNTOPTMODE_CMD             0x00000001UL                                     /**< Mode CMD for CMU_HFXOCTRL */
#define _CMU_HFXOCTRL_PEAKDETSHUNTOPTMODE_MANUAL          0x00000002UL                                     /**< Mode MANUAL for CMU_HFXOCTRL */
#define CMU_HFXOCTRL_PEAKDETSHUNTOPTMODE_DEFAULT          (_CMU_HFXOCTRL_PEAKDETSHUNTOPTMODE_DEFAULT << 4) /**< Shifted mode DEFAULT for CMU_HFXOCTRL */
#define CMU_HFXOCTRL_PEAKDETSHUNTOPTMODE_AUTOCMD          (_CMU_HFXOCTRL_PEAKDETSHUNTOPTMODE_AUTOCMD << 4) /**< Shifted mode AUTOCMD for CMU_HFXOCTRL */
#define CMU_HFXOCTRL_PEAKDETSHUNTOPTMODE_CMD              (_CMU_HFXOCTRL_PEAKDETSHUNTOPTMODE_CMD << 4)     /**< Shifted mode CMD for CMU_HFXOCTRL */
#define CMU_HFXOCTRL_PEAKDETSHUNTOPTMODE_MANUAL           (_CMU_HFXOCTRL_PEAKDETSHUNTOPTMODE_MANUAL << 4)  /**< Shifted mode MANUAL for CMU_HFXOCTRL */
#define CMU_HFXOCTRL_LOWPOWER                             (0x1UL << 8)                                     /**< Low Power Mode Control */
#define _CMU_HFXOCTRL_LOWPOWER_SHIFT                      8                                                /**< Shift value for CMU_LOWPOWER */
#define _CMU_HFXOCTRL_LOWPOWER_MASK                       0x100UL                                          /**< Bit mask for CMU_LOWPOWER */
#define _CMU_HFXOCTRL_LOWPOWER_DEFAULT                    0x00000000UL                                     /**< Mode DEFAULT for CMU_HFXOCTRL */
#define CMU_HFXOCTRL_LOWPOWER_DEFAULT                     (_CMU_HFXOCTRL_LOWPOWER_DEFAULT << 8)            /**< Shifted mode DEFAULT for CMU_HFXOCTRL */
#define CMU_HFXOCTRL_XTI2GND                              (0x1UL << 9)                                     /**< Clamp HFXTAL_N Pin to Ground When HFXO Oscillator is Off */
#define _CMU_HFXOCTRL_XTI2GND_SHIFT                       9                                                /**< Shift value for CMU_XTI2GND */
#define _CMU_HFXOCTRL_XTI2GND_MASK                        0x200UL                                          /**< Bit mask for CMU_XTI2GND */
#define _CMU_HFXOCTRL_XTI2GND_DEFAULT                     0x00000000UL                                     /**< Mode DEFAULT for CMU_HFXOCTRL */
#define CMU_HFXOCTRL_XTI2GND_DEFAULT                      (_CMU_HFXOCTRL_XTI2GND_DEFAULT << 9)             /**< Shifted mode DEFAULT for CMU_HFXOCTRL */
#define CMU_HFXOCTRL_XTO2GND                              (0x1UL << 10)                                    /**< Clamp HFXTAL_P Pin to Ground When HFXO Oscillator is Off */
#define _CMU_HFXOCTRL_XTO2GND_SHIFT                       10                                               /**< Shift value for CMU_XTO2GND */
#define _CMU_HFXOCTRL_XTO2GND_MASK                        0x400UL                                          /**< Bit mask for CMU_XTO2GND */
#define _CMU_HFXOCTRL_XTO2GND_DEFAULT                     0x00000000UL                                     /**< Mode DEFAULT for CMU_HFXOCTRL */
#define CMU_HFXOCTRL_XTO2GND_DEFAULT                      (_CMU_HFXOCTRL_XTO2GND_DEFAULT << 10)            /**< Shifted mode DEFAULT for CMU_HFXOCTRL */
#define _CMU_HFXOCTRL_LFTIMEOUT_SHIFT                     24                                               /**< Shift value for CMU_LFTIMEOUT */
#define _CMU_HFXOCTRL_LFTIMEOUT_MASK                      0x7000000UL                                      /**< Bit mask for CMU_LFTIMEOUT */
#define _CMU_HFXOCTRL_LFTIMEOUT_DEFAULT                   0x00000000UL                                     /**< Mode DEFAULT for CMU_HFXOCTRL */
#define _CMU_HFXOCTRL_LFTIMEOUT_0CYCLES                   0x00000000UL                                     /**< Mode 0CYCLES for CMU_HFXOCTRL */
#define _CMU_HFXOCTRL_LFTIMEOUT_2CYCLES                   0x00000001UL                                     /**< Mode 2CYCLES for CMU_HFXOCTRL */
#define _CMU_HFXOCTRL_LFTIMEOUT_4CYCLES                   0x00000002UL                                     /**< Mode 4CYCLES for CMU_HFXOCTRL */
#define _CMU_HFXOCTRL_LFTIMEOUT_16CYCLES                  0x00000003UL                                     /**< Mode 16CYCLES for CMU_HFXOCTRL */
#define _CMU_HFXOCTRL_LFTIMEOUT_32CYCLES                  0x00000004UL                                     /**< Mode 32CYCLES for CMU_HFXOCTRL */
#define _CMU_HFXOCTRL_LFTIMEOUT_64CYCLES                  0x00000005UL                                     /**< Mode 64CYCLES for CMU_HFXOCTRL */
#define _CMU_HFXOCTRL_LFTIMEOUT_1KCYCLES                  0x00000006UL                                     /**< Mode 1KCYCLES for CMU_HFXOCTRL */
#define _CMU_HFXOCTRL_LFTIMEOUT_4KCYCLES                  0x00000007UL                                     /**< Mode 4KCYCLES for CMU_HFXOCTRL */
#define CMU_HFXOCTRL_LFTIMEOUT_DEFAULT                    (_CMU_HFXOCTRL_LFTIMEOUT_DEFAULT << 24)          /**< Shifted mode DEFAULT for CMU_HFXOCTRL */
#define CMU_HFXOCTRL_LFTIMEOUT_0CYCLES                    (_CMU_HFXOCTRL_LFTIMEOUT_0CYCLES << 24)          /**< Shifted mode 0CYCLES for CMU_HFXOCTRL */
#define CMU_HFXOCTRL_LFTIMEOUT_2CYCLES                    (_CMU_HFXOCTRL_LFTIMEOUT_2CYCLES << 24)          /**< Shifted mode 2CYCLES for CMU_HFXOCTRL */
#define CMU_HFXOCTRL_LFTIMEOUT_4CYCLES                    (_CMU_HFXOCTRL_LFTIMEOUT_4CYCLES << 24)          /**< Shifted mode 4CYCLES for CMU_HFXOCTRL */
#define CMU_HFXOCTRL_LFTIMEOUT_16CYCLES                   (_CMU_HFXOCTRL_LFTIMEOUT_16CYCLES << 24)         /**< Shifted mode 16CYCLES for CMU_HFXOCTRL */
#define CMU_HFXOCTRL_LFTIMEOUT_32CYCLES                   (_CMU_HFXOCTRL_LFTIMEOUT_32CYCLES << 24)         /**< Shifted mode 32CYCLES for CMU_HFXOCTRL */
#define CMU_HFXOCTRL_LFTIMEOUT_64CYCLES                   (_CMU_HFXOCTRL_LFTIMEOUT_64CYCLES << 24)         /**< Shifted mode 64CYCLES for CMU_HFXOCTRL */
#define CMU_HFXOCTRL_LFTIMEOUT_1KCYCLES                   (_CMU_HFXOCTRL_LFTIMEOUT_1KCYCLES << 24)         /**< Shifted mode 1KCYCLES for CMU_HFXOCTRL */
#define CMU_HFXOCTRL_LFTIMEOUT_4KCYCLES                   (_CMU_HFXOCTRL_LFTIMEOUT_4KCYCLES << 24)         /**< Shifted mode 4KCYCLES for CMU_HFXOCTRL */
#define CMU_HFXOCTRL_AUTOSTARTEM0EM1                      (0x1UL << 28)                                    /**< Automatically Start of HFXO Upon EM0/EM1 Entry From EM2/EM3 */
#define _CMU_HFXOCTRL_AUTOSTARTEM0EM1_SHIFT               28                                               /**< Shift value for CMU_AUTOSTARTEM0EM1 */
#define _CMU_HFXOCTRL_AUTOSTARTEM0EM1_MASK                0x10000000UL                                     /**< Bit mask for CMU_AUTOSTARTEM0EM1 */
#define _CMU_HFXOCTRL_AUTOSTARTEM0EM1_DEFAULT             0x00000000UL                                     /**< Mode DEFAULT for CMU_HFXOCTRL */
#define CMU_HFXOCTRL_AUTOSTARTEM0EM1_DEFAULT              (_CMU_HFXOCTRL_AUTOSTARTEM0EM1_DEFAULT << 28)    /**< Shifted mode DEFAULT for CMU_HFXOCTRL */
#define CMU_HFXOCTRL_AUTOSTARTSELEM0EM1                   (0x1UL << 29)                                    /**< Automatically Start and Select of HFXO Upon EM0/EM1 Entry From EM2/EM3 */
#define _CMU_HFXOCTRL_AUTOSTARTSELEM0EM1_SHIFT            29                                               /**< Shift value for CMU_AUTOSTARTSELEM0EM1 */
#define _CMU_HFXOCTRL_AUTOSTARTSELEM0EM1_MASK             0x20000000UL                                     /**< Bit mask for CMU_AUTOSTARTSELEM0EM1 */
#define _CMU_HFXOCTRL_AUTOSTARTSELEM0EM1_DEFAULT          0x00000000UL                                     /**< Mode DEFAULT for CMU_HFXOCTRL */
#define CMU_HFXOCTRL_AUTOSTARTSELEM0EM1_DEFAULT           (_CMU_HFXOCTRL_AUTOSTARTSELEM0EM1_DEFAULT << 29) /**< Shifted mode DEFAULT for CMU_HFXOCTRL */

/* Bit fields for CMU HFXOCTRL1 */
#define _CMU_HFXOCTRL1_RESETVALUE                         0x00000240UL                             /**< Default value for CMU_HFXOCTRL1 */
#define _CMU_HFXOCTRL1_MASK                               0x00000277UL                             /**< Mask for CMU_HFXOCTRL1 */
#define _CMU_HFXOCTRL1_PEAKDETTHR_SHIFT                   0                                        /**< Shift value for CMU_PEAKDETTHR */
#define _CMU_HFXOCTRL1_PEAKDETTHR_MASK                    0x7UL                                    /**< Bit mask for CMU_PEAKDETTHR */
#define _CMU_HFXOCTRL1_PEAKDETTHR_DEFAULT                 0x00000000UL                             /**< Mode DEFAULT for CMU_HFXOCTRL1 */
#define CMU_HFXOCTRL1_PEAKDETTHR_DEFAULT                  (_CMU_HFXOCTRL1_PEAKDETTHR_DEFAULT << 0) /**< Shifted mode DEFAULT for CMU_HFXOCTRL1 */
#define _CMU_HFXOCTRL1_REGLVL_SHIFT                       4                                        /**< Shift value for CMU_REGLVL */
#define _CMU_HFXOCTRL1_REGLVL_MASK                        0x70UL                                   /**< Bit mask for CMU_REGLVL */
#define _CMU_HFXOCTRL1_REGLVL_DEFAULT                     0x00000004UL                             /**< Mode DEFAULT for CMU_HFXOCTRL1 */
#define CMU_HFXOCTRL1_REGLVL_DEFAULT                      (_CMU_HFXOCTRL1_REGLVL_DEFAULT << 4)     /**< Shifted mode DEFAULT for CMU_HFXOCTRL1 */
#define CMU_HFXOCTRL1_XTIBIASEN                           (0x1UL << 9)                             /**< Reserved for internal use. Do not change. */
#define _CMU_HFXOCTRL1_XTIBIASEN_SHIFT                    9                                        /**< Shift value for CMU_XTIBIASEN */
#define _CMU_HFXOCTRL1_XTIBIASEN_MASK                     0x200UL                                  /**< Bit mask for CMU_XTIBIASEN */
#define _CMU_HFXOCTRL1_XTIBIASEN_DEFAULT                  0x00000001UL                             /**< Mode DEFAULT for CMU_HFXOCTRL1 */
#define CMU_HFXOCTRL1_XTIBIASEN_DEFAULT                   (_CMU_HFXOCTRL1_XTIBIASEN_DEFAULT << 9)  /**< Shifted mode DEFAULT for CMU_HFXOCTRL1 */

/* Bit fields for CMU HFXOSTARTUPCTRL */
#define _CMU_HFXOSTARTUPCTRL_RESETVALUE                   0xA1250060UL                                     /**< Default value for CMU_HFXOSTARTUPCTRL */
#define _CMU_HFXOSTARTUPCTRL_MASK                         0xFFEFF87FUL                                     /**< Mask for CMU_HFXOSTARTUPCTRL */
#define _CMU_HFXOSTARTUPCTRL_IBTRIMXOCORE_SHIFT           0                                                /**< Shift value for CMU_IBTRIMXOCORE */
#define _CMU_HFXOSTARTUPCTRL_IBTRIMXOCORE_MASK            0x7FUL                                           /**< Bit mask for CMU_IBTRIMXOCORE */
#define _CMU_HFXOSTARTUPCTRL_IBTRIMXOCORE_DEFAULT         0x00000060UL                                     /**< Mode DEFAULT for CMU_HFXOSTARTUPCTRL */
#define CMU_HFXOSTARTUPCTRL_IBTRIMXOCORE_DEFAULT          (_CMU_HFXOSTARTUPCTRL_IBTRIMXOCORE_DEFAULT << 0) /**< Shifted mode DEFAULT for CMU_HFXOSTARTUPCTRL */
#define _CMU_HFXOSTARTUPCTRL_CTUNE_SHIFT                  11                                               /**< Shift value for CMU_CTUNE */
#define _CMU_HFXOSTARTUPCTRL_CTUNE_MASK                   0xFF800UL                                        /**< Bit mask for CMU_CTUNE */
#define _CMU_HFXOSTARTUPCTRL_CTUNE_DEFAULT                0x000000A0UL                                     /**< Mode DEFAULT for CMU_HFXOSTARTUPCTRL */
#define CMU_HFXOSTARTUPCTRL_CTUNE_DEFAULT                 (_CMU_HFXOSTARTUPCTRL_CTUNE_DEFAULT << 11)       /**< Shifted mode DEFAULT for CMU_HFXOSTARTUPCTRL */
#define _CMU_HFXOSTARTUPCTRL_RESERVED0_SHIFT              21                                               /**< Shift value for CMU_RESERVED0 */
#define _CMU_HFXOSTARTUPCTRL_RESERVED0_MASK               0xFE00000UL                                      /**< Bit mask for CMU_RESERVED0 */
#define _CMU_HFXOSTARTUPCTRL_RESERVED0_DEFAULT            0x00000009UL                                     /**< Mode DEFAULT for CMU_HFXOSTARTUPCTRL */
#define CMU_HFXOSTARTUPCTRL_RESERVED0_DEFAULT             (_CMU_HFXOSTARTUPCTRL_RESERVED0_DEFAULT << 21)   /**< Shifted mode DEFAULT for CMU_HFXOSTARTUPCTRL */
#define _CMU_HFXOSTARTUPCTRL_RESERVED1_SHIFT              28                                               /**< Shift value for CMU_RESERVED1 */
#define _CMU_HFXOSTARTUPCTRL_RESERVED1_MASK               0xF0000000UL                                     /**< Bit mask for CMU_RESERVED1 */
#define _CMU_HFXOSTARTUPCTRL_RESERVED1_DEFAULT            0x0000000AUL                                     /**< Mode DEFAULT for CMU_HFXOSTARTUPCTRL */
#define CMU_HFXOSTARTUPCTRL_RESERVED1_DEFAULT             (_CMU_HFXOSTARTUPCTRL_RESERVED1_DEFAULT << 28)   /**< Shifted mode DEFAULT for CMU_HFXOSTARTUPCTRL */

/* Bit fields for CMU HFXOSTEADYSTATECTRL */
#define _CMU_HFXOSTEADYSTATECTRL_RESETVALUE               0xA30AAD09UL                                         /**< Default value for CMU_HFXOSTEADYSTATECTRL */
#define _CMU_HFXOSTEADYSTATECTRL_MASK                     0xF70FFFFFUL                                         /**< Mask for CMU_HFXOSTEADYSTATECTRL */
#define _CMU_HFXOSTEADYSTATECTRL_IBTRIMXOCORE_SHIFT       0                                                    /**< Shift value for CMU_IBTRIMXOCORE */
#define _CMU_HFXOSTEADYSTATECTRL_IBTRIMXOCORE_MASK        0x7FUL                                               /**< Bit mask for CMU_IBTRIMXOCORE */
#define _CMU_HFXOSTEADYSTATECTRL_IBTRIMXOCORE_DEFAULT     0x00000009UL                                         /**< Mode DEFAULT for CMU_HFXOSTEADYSTATECTRL */
#define CMU_HFXOSTEADYSTATECTRL_IBTRIMXOCORE_DEFAULT      (_CMU_HFXOSTEADYSTATECTRL_IBTRIMXOCORE_DEFAULT << 0) /**< Shifted mode DEFAULT for CMU_HFXOSTEADYSTATECTRL */
#define _CMU_HFXOSTEADYSTATECTRL_REGISH_SHIFT             7                                                    /**< Shift value for CMU_REGISH */
#define _CMU_HFXOSTEADYSTATECTRL_REGISH_MASK              0x780UL                                              /**< Bit mask for CMU_REGISH */
#define _CMU_HFXOSTEADYSTATECTRL_REGISH_DEFAULT           0x0000000AUL                                         /**< Mode DEFAULT for CMU_HFXOSTEADYSTATECTRL */
#define CMU_HFXOSTEADYSTATECTRL_REGISH_DEFAULT            (_CMU_HFXOSTEADYSTATECTRL_REGISH_DEFAULT << 7)       /**< Shifted mode DEFAULT for CMU_HFXOSTEADYSTATECTRL */
#define _CMU_HFXOSTEADYSTATECTRL_CTUNE_SHIFT              11                                                   /**< Shift value for CMU_CTUNE */
#define _CMU_HFXOSTEADYSTATECTRL_CTUNE_MASK               0xFF800UL                                            /**< Bit mask for CMU_CTUNE */
#define _CMU_HFXOSTEADYSTATECTRL_CTUNE_DEFAULT            0x00000155UL                                         /**< Mode DEFAULT for CMU_HFXOSTEADYSTATECTRL */
#define CMU_HFXOSTEADYSTATECTRL_CTUNE_DEFAULT             (_CMU_HFXOSTEADYSTATECTRL_CTUNE_DEFAULT << 11)       /**< Shifted mode DEFAULT for CMU_HFXOSTEADYSTATECTRL */
#define _CMU_HFXOSTEADYSTATECTRL_REGSELILOW_SHIFT         24                                                   /**< Shift value for CMU_REGSELILOW */
#define _CMU_HFXOSTEADYSTATECTRL_REGSELILOW_MASK          0x3000000UL                                          /**< Bit mask for CMU_REGSELILOW */
#define _CMU_HFXOSTEADYSTATECTRL_REGSELILOW_DEFAULT       0x00000003UL                                         /**< Mode DEFAULT for CMU_HFXOSTEADYSTATECTRL */
#define CMU_HFXOSTEADYSTATECTRL_REGSELILOW_DEFAULT        (_CMU_HFXOSTEADYSTATECTRL_REGSELILOW_DEFAULT << 24)  /**< Shifted mode DEFAULT for CMU_HFXOSTEADYSTATECTRL */
#define CMU_HFXOSTEADYSTATECTRL_PEAKDETEN                 (0x1UL << 26)                                        /**< Enables Oscillator Peak Detectors */
#define _CMU_HFXOSTEADYSTATECTRL_PEAKDETEN_SHIFT          26                                                   /**< Shift value for CMU_PEAKDETEN */
#define _CMU_HFXOSTEADYSTATECTRL_PEAKDETEN_MASK           0x4000000UL                                          /**< Bit mask for CMU_PEAKDETEN */
#define _CMU_HFXOSTEADYSTATECTRL_PEAKDETEN_DEFAULT        0x00000000UL                                         /**< Mode DEFAULT for CMU_HFXOSTEADYSTATECTRL */
#define CMU_HFXOSTEADYSTATECTRL_PEAKDETEN_DEFAULT         (_CMU_HFXOSTEADYSTATECTRL_PEAKDETEN_DEFAULT << 26)   /**< Shifted mode DEFAULT for CMU_HFXOSTEADYSTATECTRL */
#define _CMU_HFXOSTEADYSTATECTRL_REGISHUPPER_SHIFT        28                                                   /**< Shift value for CMU_REGISHUPPER */
#define _CMU_HFXOSTEADYSTATECTRL_REGISHUPPER_MASK         0xF0000000UL                                         /**< Bit mask for CMU_REGISHUPPER */
#define _CMU_HFXOSTEADYSTATECTRL_REGISHUPPER_DEFAULT      0x0000000AUL                                         /**< Mode DEFAULT for CMU_HFXOSTEADYSTATECTRL */
#define CMU_HFXOSTEADYSTATECTRL_REGISHUPPER_DEFAULT       (_CMU_HFXOSTEADYSTATECTRL_REGISHUPPER_DEFAULT << 28) /**< Shifted mode DEFAULT for CMU_HFXOSTEADYSTATECTRL */

/* Bit fields for CMU HFXOTIMEOUTCTRL */
#define _CMU_HFXOTIMEOUTCTRL_RESETVALUE                   0x00026667UL                                           /**< Default value for CMU_HFXOTIMEOUTCTRL */
#define _CMU_HFXOTIMEOUTCTRL_MASK                         0x000FFFFFUL                                           /**< Mask for CMU_HFXOTIMEOUTCTRL */
#define _CMU_HFXOTIMEOUTCTRL_STARTUPTIMEOUT_SHIFT         0                                                      /**< Shift value for CMU_STARTUPTIMEOUT */
#define _CMU_HFXOTIMEOUTCTRL_STARTUPTIMEOUT_MASK          0xFUL                                                  /**< Bit mask for CMU_STARTUPTIMEOUT */
#define _CMU_HFXOTIMEOUTCTRL_STARTUPTIMEOUT_2CYCLES       0x00000000UL                                           /**< Mode 2CYCLES for CMU_HFXOTIMEOUTCTRL */
#define _CMU_HFXOTIMEOUTCTRL_STARTUPTIMEOUT_4CYCLES       0x00000001UL                                           /**< Mode 4CYCLES for CMU_HFXOTIMEOUTCTRL */
#define _CMU_HFXOTIMEOUTCTRL_STARTUPTIMEOUT_16CYCLES      0x00000002UL                                           /**< Mode 16CYCLES for CMU_HFXOTIMEOUTCTRL */
#define _CMU_HFXOTIMEOUTCTRL_STARTUPTIMEOUT_32CYCLES      0x00000003UL                                           /**< Mode 32CYCLES for CMU_HFXOTIMEOUTCTRL */
#define _CMU_HFXOTIMEOUTCTRL_STARTUPTIMEOUT_256CYCLES     0x00000004UL                                           /**< Mode 256CYCLES for CMU_HFXOTIMEOUTCTRL */
#define _CMU_HFXOTIMEOUTCTRL_STARTUPTIMEOUT_1KCYCLES      0x00000005UL                                           /**< Mode 1KCYCLES for CMU_HFXOTIMEOUTCTRL */
#define _CMU_HFXOTIMEOUTCTRL_STARTUPTIMEOUT_2KCYCLES      0x00000006UL                                           /**< Mode 2KCYCLES for CMU_HFXOTIMEOUTCTRL */
#define _CMU_HFXOTIMEOUTCTRL_STARTUPTIMEOUT_DEFAULT       0x00000007UL                                           /**< Mode DEFAULT for CMU_HFXOTIMEOUTCTRL */
#define _CMU_HFXOTIMEOUTCTRL_STARTUPTIMEOUT_4KCYCLES      0x00000007UL                                           /**< Mode 4KCYCLES for CMU_HFXOTIMEOUTCTRL */
#define _CMU_HFXOTIMEOUTCTRL_STARTUPTIMEOUT_8KCYCLES      0x00000008UL                                           /**< Mode 8KCYCLES for CMU_HFXOTIMEOUTCTRL */
#define _CMU_HFXOTIMEOUTCTRL_STARTUPTIMEOUT_16KCYCLES     0x00000009UL                                           /**< Mode 16KCYCLES for CMU_HFXOTIMEOUTCTRL */
#define _CMU_HFXOTIMEOUTCTRL_STARTUPTIMEOUT_32KCYCLES     0x0000000AUL                                           /**< Mode 32KCYCLES for CMU_HFXOTIMEOUTCTRL */
#define CMU_HFXOTIMEOUTCTRL_STARTUPTIMEOUT_2CYCLES        (_CMU_HFXOTIMEOUTCTRL_STARTUPTIMEOUT_2CYCLES << 0)     /**< Shifted mode 2CYCLES for CMU_HFXOTIMEOUTCTRL */
#define CMU_HFXOTIMEOUTCTRL_STARTUPTIMEOUT_4CYCLES        (_CMU_HFXOTIMEOUTCTRL_STARTUPTIMEOUT_4CYCLES << 0)     /**< Shifted mode 4CYCLES for CMU_HFXOTIMEOUTCTRL */
#define CMU_HFXOTIMEOUTCTRL_STARTUPTIMEOUT_16CYCLES       (_CMU_HFXOTIMEOUTCTRL_STARTUPTIMEOUT_16CYCLES << 0)    /**< Shifted mode 16CYCLES for CMU_HFXOTIMEOUTCTRL */
#define CMU_HFXOTIMEOUTCTRL_STARTUPTIMEOUT_32CYCLES       (_CMU_HFXOTIMEOUTCTRL_STARTUPTIMEOUT_32CYCLES << 0)    /**< Shifted mode 32CYCLES for CMU_HFXOTIMEOUTCTRL */
#define CMU_HFXOTIMEOUTCTRL_STARTUPTIMEOUT_256CYCLES      (_CMU_HFXOTIMEOUTCTRL_STARTUPTIMEOUT_256CYCLES << 0)   /**< Shifted mode 256CYCLES for CMU_HFXOTIMEOUTCTRL */
#define CMU_HFXOTIMEOUTCTRL_STARTUPTIMEOUT_1KCYCLES       (_CMU_HFXOTIMEOUTCTRL_STARTUPTIMEOUT_1KCYCLES << 0)    /**< Shifted mode 1KCYCLES for CMU_HFXOTIMEOUTCTRL */
#define CMU_HFXOTIMEOUTCTRL_STARTUPTIMEOUT_2KCYCLES       (_CMU_HFXOTIMEOUTCTRL_STARTUPTIMEOUT_2KCYCLES << 0)    /**< Shifted mode 2KCYCLES for CMU_HFXOTIMEOUTCTRL */
#define CMU_HFXOTIMEOUTCTRL_STARTUPTIMEOUT_DEFAULT        (_CMU_HFXOTIMEOUTCTRL_STARTUPTIMEOUT_DEFAULT << 0)     /**< Shifted mode DEFAULT for CMU_HFXOTIMEOUTCTRL */
#define CMU_HFXOTIMEOUTCTRL_STARTUPTIMEOUT_4KCYCLES       (_CMU_HFXOTIMEOUTCTRL_STARTUPTIMEOUT_4KCYCLES << 0)    /**< Shifted mode 4KCYCLES for CMU_HFXOTIMEOUTCTRL */
#define CMU_HFXOTIMEOUTCTRL_STARTUPTIMEOUT_8KCYCLES       (_CMU_HFXOTIMEOUTCTRL_STARTUPTIMEOUT_8KCYCLES << 0)    /**< Shifted mode 8KCYCLES for CMU_HFXOTIMEOUTCTRL */
#define CMU_HFXOTIMEOUTCTRL_STARTUPTIMEOUT_16KCYCLES      (_CMU_HFXOTIMEOUTCTRL_STARTUPTIMEOUT_16KCYCLES << 0)   /**< Shifted mode 16KCYCLES for CMU_HFXOTIMEOUTCTRL */
#define CMU_HFXOTIMEOUTCTRL_STARTUPTIMEOUT_32KCYCLES      (_CMU_HFXOTIMEOUTCTRL_STARTUPTIMEOUT_32KCYCLES << 0)   /**< Shifted mode 32KCYCLES for CMU_HFXOTIMEOUTCTRL */
#define _CMU_HFXOTIMEOUTCTRL_STEADYTIMEOUT_SHIFT          4                                                      /**< Shift value for CMU_STEADYTIMEOUT */
#define _CMU_HFXOTIMEOUTCTRL_STEADYTIMEOUT_MASK           0xF0UL                                                 /**< Bit mask for CMU_STEADYTIMEOUT */
#define _CMU_HFXOTIMEOUTCTRL_STEADYTIMEOUT_2CYCLES        0x00000000UL                                           /**< Mode 2CYCLES for CMU_HFXOTIMEOUTCTRL */
#define _CMU_HFXOTIMEOUTCTRL_STEADYTIMEOUT_4CYCLES        0x00000001UL                                           /**< Mode 4CYCLES for CMU_HFXOTIMEOUTCTRL */
#define _CMU_HFXOTIMEOUTCTRL_STEADYTIMEOUT_16CYCLES       0x00000002UL                                           /**< Mode 16CYCLES for CMU_HFXOTIMEOUTCTRL */
#define _CMU_HFXOTIMEOUTCTRL_STEADYTIMEOUT_32CYCLES       0x00000003UL                                           /**< Mode 32CYCLES for CMU_HFXOTIMEOUTCTRL */
#define _CMU_HFXOTIMEOUTCTRL_STEADYTIMEOUT_256CYCLES      0x00000004UL                                           /**< Mode 256CYCLES for CMU_HFXOTIMEOUTCTRL */
#define _CMU_HFXOTIMEOUTCTRL_STEADYTIMEOUT_1KCYCLES       0x00000005UL                                           /**< Mode 1KCYCLES for CMU_HFXOTIMEOUTCTRL */
#define _CMU_HFXOTIMEOUTCTRL_STEADYTIMEOUT_DEFAULT        0x00000006UL                                           /**< Mode DEFAULT for CMU_HFXOTIMEOUTCTRL */
#define _CMU_HFXOTIMEOUTCTRL_STEADYTIMEOUT_2KCYCLES       0x00000006UL                                           /**< Mode 2KCYCLES for CMU_HFXOTIMEOUTCTRL */
#define _CMU_HFXOTIMEOUTCTRL_STEADYTIMEOUT_4KCYCLES       0x00000007UL                                           /**< Mode 4KCYCLES for CMU_HFXOTIMEOUTCTRL */
#define _CMU_HFXOTIMEOUTCTRL_STEADYTIMEOUT_8KCYCLES       0x00000008UL                                           /**< Mode 8KCYCLES for CMU_HFXOTIMEOUTCTRL */
#define _CMU_HFXOTIMEOUTCTRL_STEADYTIMEOUT_16KCYCLES      0x00000009UL                                           /**< Mode 16KCYCLES for CMU_HFXOTIMEOUTCTRL */
#define _CMU_HFXOTIMEOUTCTRL_STEADYTIMEOUT_32KCYCLES      0x0000000AUL                                           /**< Mode 32KCYCLES for CMU_HFXOTIMEOUTCTRL */
#define CMU_HFXOTIMEOUTCTRL_STEADYTIMEOUT_2CYCLES         (_CMU_HFXOTIMEOUTCTRL_STEADYTIMEOUT_2CYCLES << 4)      /**< Shifted mode 2CYCLES for CMU_HFXOTIMEOUTCTRL */
#define CMU_HFXOTIMEOUTCTRL_STEADYTIMEOUT_4CYCLES         (_CMU_HFXOTIMEOUTCTRL_STEADYTIMEOUT_4CYCLES << 4)      /**< Shifted mode 4CYCLES for CMU_HFXOTIMEOUTCTRL */
#define CMU_HFXOTIMEOUTCTRL_STEADYTIMEOUT_16CYCLES        (_CMU_HFXOTIMEOUTCTRL_STEADYTIMEOUT_16CYCLES << 4)     /**< Shifted mode 16CYCLES for CMU_HFXOTIMEOUTCTRL */
#define CMU_HFXOTIMEOUTCTRL_STEADYTIMEOUT_32CYCLES        (_CMU_HFXOTIMEOUTCTRL_STEADYTIMEOUT_32CYCLES << 4)     /**< Shifted mode 32CYCLES for CMU_HFXOTIMEOUTCTRL */
#define CMU_HFXOTIMEOUTCTRL_STEADYTIMEOUT_256CYCLES       (_CMU_HFXOTIMEOUTCTRL_STEADYTIMEOUT_256CYCLES << 4)    /**< Shifted mode 256CYCLES for CMU_HFXOTIMEOUTCTRL */
#define CMU_HFXOTIMEOUTCTRL_STEADYTIMEOUT_1KCYCLES        (_CMU_HFXOTIMEOUTCTRL_STEADYTIMEOUT_1KCYCLES << 4)     /**< Shifted mode 1KCYCLES for CMU_HFXOTIMEOUTCTRL */
#define CMU_HFXOTIMEOUTCTRL_STEADYTIMEOUT_DEFAULT         (_CMU_HFXOTIMEOUTCTRL_STEADYTIMEOUT_DEFAULT << 4)      /**< Shifted mode DEFAULT for CMU_HFXOTIMEOUTCTRL */
#define CMU_HFXOTIMEOUTCTRL_STEADYTIMEOUT_2KCYCLES        (_CMU_HFXOTIMEOUTCTRL_STEADYTIMEOUT_2KCYCLES << 4)     /**< Shifted mode 2KCYCLES for CMU_HFXOTIMEOUTCTRL */
#define CMU_HFXOTIMEOUTCTRL_STEADYTIMEOUT_4KCYCLES        (_CMU_HFXOTIMEOUTCTRL_STEADYTIMEOUT_4KCYCLES << 4)     /**< Shifted mode 4KCYCLES for CMU_HFXOTIMEOUTCTRL */
#define CMU_HFXOTIMEOUTCTRL_STEADYTIMEOUT_8KCYCLES        (_CMU_HFXOTIMEOUTCTRL_STEADYTIMEOUT_8KCYCLES << 4)     /**< Shifted mode 8KCYCLES for CMU_HFXOTIMEOUTCTRL */
#define CMU_HFXOTIMEOUTCTRL_STEADYTIMEOUT_16KCYCLES       (_CMU_HFXOTIMEOUTCTRL_STEADYTIMEOUT_16KCYCLES << 4)    /**< Shifted mode 16KCYCLES for CMU_HFXOTIMEOUTCTRL */
#define CMU_HFXOTIMEOUTCTRL_STEADYTIMEOUT_32KCYCLES       (_CMU_HFXOTIMEOUTCTRL_STEADYTIMEOUT_32KCYCLES << 4)    /**< Shifted mode 32KCYCLES for CMU_HFXOTIMEOUTCTRL */
#define _CMU_HFXOTIMEOUTCTRL_RESERVED2_SHIFT              8                                                      /**< Shift value for CMU_RESERVED2 */
#define _CMU_HFXOTIMEOUTCTRL_RESERVED2_MASK               0xF00UL                                                /**< Bit mask for CMU_RESERVED2 */
#define _CMU_HFXOTIMEOUTCTRL_RESERVED2_DEFAULT            0x00000006UL                                           /**< Mode DEFAULT for CMU_HFXOTIMEOUTCTRL */
#define CMU_HFXOTIMEOUTCTRL_RESERVED2_DEFAULT             (_CMU_HFXOTIMEOUTCTRL_RESERVED2_DEFAULT << 8)          /**< Shifted mode DEFAULT for CMU_HFXOTIMEOUTCTRL */
#define _CMU_HFXOTIMEOUTCTRL_PEAKDETTIMEOUT_SHIFT         12                                                     /**< Shift value for CMU_PEAKDETTIMEOUT */
#define _CMU_HFXOTIMEOUTCTRL_PEAKDETTIMEOUT_MASK          0xF000UL                                               /**< Bit mask for CMU_PEAKDETTIMEOUT */
#define _CMU_HFXOTIMEOUTCTRL_PEAKDETTIMEOUT_2CYCLES       0x00000000UL                                           /**< Mode 2CYCLES for CMU_HFXOTIMEOUTCTRL */
#define _CMU_HFXOTIMEOUTCTRL_PEAKDETTIMEOUT_4CYCLES       0x00000001UL                                           /**< Mode 4CYCLES for CMU_HFXOTIMEOUTCTRL */
#define _CMU_HFXOTIMEOUTCTRL_PEAKDETTIMEOUT_16CYCLES      0x00000002UL                                           /**< Mode 16CYCLES for CMU_HFXOTIMEOUTCTRL */
#define _CMU_HFXOTIMEOUTCTRL_PEAKDETTIMEOUT_32CYCLES      0x00000003UL                                           /**< Mode 32CYCLES for CMU_HFXOTIMEOUTCTRL */
#define _CMU_HFXOTIMEOUTCTRL_PEAKDETTIMEOUT_256CYCLES     0x00000004UL                                           /**< Mode 256CYCLES for CMU_HFXOTIMEOUTCTRL */
#define _CMU_HFXOTIMEOUTCTRL_PEAKDETTIMEOUT_1KCYCLES      0x00000005UL                                           /**< Mode 1KCYCLES for CMU_HFXOTIMEOUTCTRL */
#define _CMU_HFXOTIMEOUTCTRL_PEAKDETTIMEOUT_DEFAULT       0x00000006UL                                           /**< Mode DEFAULT for CMU_HFXOTIMEOUTCTRL */
#define _CMU_HFXOTIMEOUTCTRL_PEAKDETTIMEOUT_2KCYCLES      0x00000006UL                                           /**< Mode 2KCYCLES for CMU_HFXOTIMEOUTCTRL */
#define _CMU_HFXOTIMEOUTCTRL_PEAKDETTIMEOUT_4KCYCLES      0x00000007UL                                           /**< Mode 4KCYCLES for CMU_HFXOTIMEOUTCTRL */
#define _CMU_HFXOTIMEOUTCTRL_PEAKDETTIMEOUT_8KCYCLES      0x00000008UL                                           /**< Mode 8KCYCLES for CMU_HFXOTIMEOUTCTRL */
#define _CMU_HFXOTIMEOUTCTRL_PEAKDETTIMEOUT_16KCYCLES     0x00000009UL                                           /**< Mode 16KCYCLES for CMU_HFXOTIMEOUTCTRL */
#define _CMU_HFXOTIMEOUTCTRL_PEAKDETTIMEOUT_32KCYCLES     0x0000000AUL                                           /**< Mode 32KCYCLES for CMU_HFXOTIMEOUTCTRL */
#define CMU_HFXOTIMEOUTCTRL_PEAKDETTIMEOUT_2CYCLES        (_CMU_HFXOTIMEOUTCTRL_PEAKDETTIMEOUT_2CYCLES << 12)    /**< Shifted mode 2CYCLES for CMU_HFXOTIMEOUTCTRL */
#define CMU_HFXOTIMEOUTCTRL_PEAKDETTIMEOUT_4CYCLES        (_CMU_HFXOTIMEOUTCTRL_PEAKDETTIMEOUT_4CYCLES << 12)    /**< Shifted mode 4CYCLES for CMU_HFXOTIMEOUTCTRL */
#define CMU_HFXOTIMEOUTCTRL_PEAKDETTIMEOUT_16CYCLES       (_CMU_HFXOTIMEOUTCTRL_PEAKDETTIMEOUT_16CYCLES << 12)   /**< Shifted mode 16CYCLES for CMU_HFXOTIMEOUTCTRL */
#define CMU_HFXOTIMEOUTCTRL_PEAKDETTIMEOUT_32CYCLES       (_CMU_HFXOTIMEOUTCTRL_PEAKDETTIMEOUT_32CYCLES << 12)   /**< Shifted mode 32CYCLES for CMU_HFXOTIMEOUTCTRL */
#define CMU_HFXOTIMEOUTCTRL_PEAKDETTIMEOUT_256CYCLES      (_CMU_HFXOTIMEOUTCTRL_PEAKDETTIMEOUT_256CYCLES << 12)  /**< Shifted mode 256CYCLES for CMU_HFXOTIMEOUTCTRL */
#define CMU_HFXOTIMEOUTCTRL_PEAKDETTIMEOUT_1KCYCLES       (_CMU_HFXOTIMEOUTCTRL_PEAKDETTIMEOUT_1KCYCLES << 12)   /**< Shifted mode 1KCYCLES for CMU_HFXOTIMEOUTCTRL */
#define CMU_HFXOTIMEOUTCTRL_PEAKDETTIMEOUT_DEFAULT        (_CMU_HFXOTIMEOUTCTRL_PEAKDETTIMEOUT_DEFAULT << 12)    /**< Shifted mode DEFAULT for CMU_HFXOTIMEOUTCTRL */
#define CMU_HFXOTIMEOUTCTRL_PEAKDETTIMEOUT_2KCYCLES       (_CMU_HFXOTIMEOUTCTRL_PEAKDETTIMEOUT_2KCYCLES << 12)   /**< Shifted mode 2KCYCLES for CMU_HFXOTIMEOUTCTRL */
#define CMU_HFXOTIMEOUTCTRL_PEAKDETTIMEOUT_4KCYCLES       (_CMU_HFXOTIMEOUTCTRL_PEAKDETTIMEOUT_4KCYCLES << 12)   /**< Shifted mode 4KCYCLES for CMU_HFXOTIMEOUTCTRL */
#define CMU_HFXOTIMEOUTCTRL_PEAKDETTIMEOUT_8KCYCLES       (_CMU_HFXOTIMEOUTCTRL_PEAKDETTIMEOUT_8KCYCLES << 12)   /**< Shifted mode 8KCYCLES for CMU_HFXOTIMEOUTCTRL */
#define CMU_HFXOTIMEOUTCTRL_PEAKDETTIMEOUT_16KCYCLES      (_CMU_HFXOTIMEOUTCTRL_PEAKDETTIMEOUT_16KCYCLES << 12)  /**< Shifted mode 16KCYCLES for CMU_HFXOTIMEOUTCTRL */
#define CMU_HFXOTIMEOUTCTRL_PEAKDETTIMEOUT_32KCYCLES      (_CMU_HFXOTIMEOUTCTRL_PEAKDETTIMEOUT_32KCYCLES << 12)  /**< Shifted mode 32KCYCLES for CMU_HFXOTIMEOUTCTRL */
#define _CMU_HFXOTIMEOUTCTRL_SHUNTOPTTIMEOUT_SHIFT        16                                                     /**< Shift value for CMU_SHUNTOPTTIMEOUT */
#define _CMU_HFXOTIMEOUTCTRL_SHUNTOPTTIMEOUT_MASK         0xF0000UL                                              /**< Bit mask for CMU_SHUNTOPTTIMEOUT */
#define _CMU_HFXOTIMEOUTCTRL_SHUNTOPTTIMEOUT_2CYCLES      0x00000000UL                                           /**< Mode 2CYCLES for CMU_HFXOTIMEOUTCTRL */
#define _CMU_HFXOTIMEOUTCTRL_SHUNTOPTTIMEOUT_4CYCLES      0x00000001UL                                           /**< Mode 4CYCLES for CMU_HFXOTIMEOUTCTRL */
#define _CMU_HFXOTIMEOUTCTRL_SHUNTOPTTIMEOUT_DEFAULT      0x00000002UL                                           /**< Mode DEFAULT for CMU_HFXOTIMEOUTCTRL */
#define _CMU_HFXOTIMEOUTCTRL_SHUNTOPTTIMEOUT_16CYCLES     0x00000002UL                                           /**< Mode 16CYCLES for CMU_HFXOTIMEOUTCTRL */
#define _CMU_HFXOTIMEOUTCTRL_SHUNTOPTTIMEOUT_32CYCLES     0x00000003UL                                           /**< Mode 32CYCLES for CMU_HFXOTIMEOUTCTRL */
#define _CMU_HFXOTIMEOUTCTRL_SHUNTOPTTIMEOUT_256CYCLES    0x00000004UL                                           /**< Mode 256CYCLES for CMU_HFXOTIMEOUTCTRL */
#define _CMU_HFXOTIMEOUTCTRL_SHUNTOPTTIMEOUT_1KCYCLES     0x00000005UL                                           /**< Mode 1KCYCLES for CMU_HFXOTIMEOUTCTRL */
#define _CMU_HFXOTIMEOUTCTRL_SHUNTOPTTIMEOUT_2KCYCLES     0x00000006UL                                           /**< Mode 2KCYCLES for CMU_HFXOTIMEOUTCTRL */
#define _CMU_HFXOTIMEOUTCTRL_SHUNTOPTTIMEOUT_4KCYCLES     0x00000007UL                                           /**< Mode 4KCYCLES for CMU_HFXOTIMEOUTCTRL */
#define _CMU_HFXOTIMEOUTCTRL_SHUNTOPTTIMEOUT_8KCYCLES     0x00000008UL                                           /**< Mode 8KCYCLES for CMU_HFXOTIMEOUTCTRL */
#define _CMU_HFXOTIMEOUTCTRL_SHUNTOPTTIMEOUT_16KCYCLES    0x00000009UL                                           /**< Mode 16KCYCLES for CMU_HFXOTIMEOUTCTRL */
#define _CMU_HFXOTIMEOUTCTRL_SHUNTOPTTIMEOUT_32KCYCLES    0x0000000AUL                                           /**< Mode 32KCYCLES for CMU_HFXOTIMEOUTCTRL */
#define CMU_HFXOTIMEOUTCTRL_SHUNTOPTTIMEOUT_2CYCLES       (_CMU_HFXOTIMEOUTCTRL_SHUNTOPTTIMEOUT_2CYCLES << 16)   /**< Shifted mode 2CYCLES for CMU_HFXOTIMEOUTCTRL */
#define CMU_HFXOTIMEOUTCTRL_SHUNTOPTTIMEOUT_4CYCLES       (_CMU_HFXOTIMEOUTCTRL_SHUNTOPTTIMEOUT_4CYCLES << 16)   /**< Shifted mode 4CYCLES for CMU_HFXOTIMEOUTCTRL */
#define CMU_HFXOTIMEOUTCTRL_SHUNTOPTTIMEOUT_DEFAULT       (_CMU_HFXOTIMEOUTCTRL_SHUNTOPTTIMEOUT_DEFAULT << 16)   /**< Shifted mode DEFAULT for CMU_HFXOTIMEOUTCTRL */
#define CMU_HFXOTIMEOUTCTRL_SHUNTOPTTIMEOUT_16CYCLES      (_CMU_HFXOTIMEOUTCTRL_SHUNTOPTTIMEOUT_16CYCLES << 16)  /**< Shifted mode 16CYCLES for CMU_HFXOTIMEOUTCTRL */
#define CMU_HFXOTIMEOUTCTRL_SHUNTOPTTIMEOUT_32CYCLES      (_CMU_HFXOTIMEOUTCTRL_SHUNTOPTTIMEOUT_32CYCLES << 16)  /**< Shifted mode 32CYCLES for CMU_HFXOTIMEOUTCTRL */
#define CMU_HFXOTIMEOUTCTRL_SHUNTOPTTIMEOUT_256CYCLES     (_CMU_HFXOTIMEOUTCTRL_SHUNTOPTTIMEOUT_256CYCLES << 16) /**< Shifted mode 256CYCLES for CMU_HFXOTIMEOUTCTRL */
#define CMU_HFXOTIMEOUTCTRL_SHUNTOPTTIMEOUT_1KCYCLES      (_CMU_HFXOTIMEOUTCTRL_SHUNTOPTTIMEOUT_1KCYCLES << 16)  /**< Shifted mode 1KCYCLES for CMU_HFXOTIMEOUTCTRL */
#define CMU_HFXOTIMEOUTCTRL_SHUNTOPTTIMEOUT_2KCYCLES      (_CMU_HFXOTIMEOUTCTRL_SHUNTOPTTIMEOUT_2KCYCLES << 16)  /**< Shifted mode 2KCYCLES for CMU_HFXOTIMEOUTCTRL */
#define CMU_HFXOTIMEOUTCTRL_SHUNTOPTTIMEOUT_4KCYCLES      (_CMU_HFXOTIMEOUTCTRL_SHUNTOPTTIMEOUT_4KCYCLES << 16)  /**< Shifted mode 4KCYCLES for CMU_HFXOTIMEOUTCTRL */
#define CMU_HFXOTIMEOUTCTRL_SHUNTOPTTIMEOUT_8KCYCLES      (_CMU_HFXOTIMEOUTCTRL_SHUNTOPTTIMEOUT_8KCYCLES << 16)  /**< Shifted mode 8KCYCLES for CMU_HFXOTIMEOUTCTRL */
#define CMU_HFXOTIMEOUTCTRL_SHUNTOPTTIMEOUT_16KCYCLES     (_CMU_HFXOTIMEOUTCTRL_SHUNTOPTTIMEOUT_16KCYCLES << 16) /**< Shifted mode 16KCYCLES for CMU_HFXOTIMEOUTCTRL */
#define CMU_HFXOTIMEOUTCTRL_SHUNTOPTTIMEOUT_32KCYCLES     (_CMU_HFXOTIMEOUTCTRL_SHUNTOPTTIMEOUT_32KCYCLES << 16) /**< Shifted mode 32KCYCLES for CMU_HFXOTIMEOUTCTRL */

/* Bit fields for CMU LFXOCTRL */
#define _CMU_LFXOCTRL_RESETVALUE                          0x07009000UL                            /**< Default value for CMU_LFXOCTRL */
#define _CMU_LFXOCTRL_MASK                                0x0713DB7FUL                            /**< Mask for CMU_LFXOCTRL */
#define _CMU_LFXOCTRL_TUNING_SHIFT                        0                                       /**< Shift value for CMU_TUNING */
#define _CMU_LFXOCTRL_TUNING_MASK                         0x7FUL                                  /**< Bit mask for CMU_TUNING */
#define _CMU_LFXOCTRL_TUNING_DEFAULT                      0x00000000UL                            /**< Mode DEFAULT for CMU_LFXOCTRL */
#define CMU_LFXOCTRL_TUNING_DEFAULT                       (_CMU_LFXOCTRL_TUNING_DEFAULT << 0)     /**< Shifted mode DEFAULT for CMU_LFXOCTRL */
#define _CMU_LFXOCTRL_MODE_SHIFT                          8                                       /**< Shift value for CMU_MODE */
#define _CMU_LFXOCTRL_MODE_MASK                           0x300UL                                 /**< Bit mask for CMU_MODE */
#define _CMU_LFXOCTRL_MODE_DEFAULT                        0x00000000UL                            /**< Mode DEFAULT for CMU_LFXOCTRL */
#define _CMU_LFXOCTRL_MODE_XTAL                           0x00000000UL                            /**< Mode XTAL for CMU_LFXOCTRL */
#define _CMU_LFXOCTRL_MODE_BUFEXTCLK                      0x00000001UL                            /**< Mode BUFEXTCLK for CMU_LFXOCTRL */
#define _CMU_LFXOCTRL_MODE_DIGEXTCLK                      0x00000002UL                            /**< Mode DIGEXTCLK for CMU_LFXOCTRL */
#define CMU_LFXOCTRL_MODE_DEFAULT                         (_CMU_LFXOCTRL_MODE_DEFAULT << 8)       /**< Shifted mode DEFAULT for CMU_LFXOCTRL */
#define CMU_LFXOCTRL_MODE_XTAL                            (_CMU_LFXOCTRL_MODE_XTAL << 8)          /**< Shifted mode XTAL for CMU_LFXOCTRL */
#define CMU_LFXOCTRL_MODE_BUFEXTCLK                       (_CMU_LFXOCTRL_MODE_BUFEXTCLK << 8)     /**< Shifted mode BUFEXTCLK for CMU_LFXOCTRL */
#define CMU_LFXOCTRL_MODE_DIGEXTCLK                       (_CMU_LFXOCTRL_MODE_DIGEXTCLK << 8)     /**< Shifted mode DIGEXTCLK for CMU_LFXOCTRL */
#define _CMU_LFXOCTRL_GAIN_SHIFT                          11                                      /**< Shift value for CMU_GAIN */
#define _CMU_LFXOCTRL_GAIN_MASK                           0x1800UL                                /**< Bit mask for CMU_GAIN */
#define _CMU_LFXOCTRL_GAIN_DEFAULT                        0x00000002UL                            /**< Mode DEFAULT for CMU_LFXOCTRL */
#define CMU_LFXOCTRL_GAIN_DEFAULT                         (_CMU_LFXOCTRL_GAIN_DEFAULT << 11)      /**< Shifted mode DEFAULT for CMU_LFXOCTRL */
#define CMU_LFXOCTRL_HIGHAMPL                             (0x1UL << 14)                           /**< LFXO High XTAL Oscillation Amplitude Enable */
#define _CMU_LFXOCTRL_HIGHAMPL_SHIFT                      14                                      /**< Shift value for CMU_HIGHAMPL */
#define _CMU_LFXOCTRL_HIGHAMPL_MASK                       0x4000UL                                /**< Bit mask for CMU_HIGHAMPL */
#define _CMU_LFXOCTRL_HIGHAMPL_DEFAULT                    0x00000000UL                            /**< Mode DEFAULT for CMU_LFXOCTRL */
#define CMU_LFXOCTRL_HIGHAMPL_DEFAULT                     (_CMU_LFXOCTRL_HIGHAMPL_DEFAULT << 14)  /**< Shifted mode DEFAULT for CMU_LFXOCTRL */
#define CMU_LFXOCTRL_AGC                                  (0x1UL << 15)                           /**< LFXO AGC Enable */
#define _CMU_LFXOCTRL_AGC_SHIFT                           15                                      /**< Shift value for CMU_AGC */
#define _CMU_LFXOCTRL_AGC_MASK                            0x8000UL                                /**< Bit mask for CMU_AGC */
#define _CMU_LFXOCTRL_AGC_DEFAULT                         0x00000001UL                            /**< Mode DEFAULT for CMU_LFXOCTRL */
#define CMU_LFXOCTRL_AGC_DEFAULT                          (_CMU_LFXOCTRL_AGC_DEFAULT << 15)       /**< Shifted mode DEFAULT for CMU_LFXOCTRL */
#define _CMU_LFXOCTRL_CUR_SHIFT                           16                                      /**< Shift value for CMU_CUR */
#define _CMU_LFXOCTRL_CUR_MASK                            0x30000UL                               /**< Bit mask for CMU_CUR */
#define _CMU_LFXOCTRL_CUR_DEFAULT                         0x00000000UL                            /**< Mode DEFAULT for CMU_LFXOCTRL */
#define CMU_LFXOCTRL_CUR_DEFAULT                          (_CMU_LFXOCTRL_CUR_DEFAULT << 16)       /**< Shifted mode DEFAULT for CMU_LFXOCTRL */
#define CMU_LFXOCTRL_BUFCUR                               (0x1UL << 20)                           /**< LFXO Buffer Bias Current */
#define _CMU_LFXOCTRL_BUFCUR_SHIFT                        20                                      /**< Shift value for CMU_BUFCUR */
#define _CMU_LFXOCTRL_BUFCUR_MASK                         0x100000UL                              /**< Bit mask for CMU_BUFCUR */
#define _CMU_LFXOCTRL_BUFCUR_DEFAULT                      0x00000000UL                            /**< Mode DEFAULT for CMU_LFXOCTRL */
#define CMU_LFXOCTRL_BUFCUR_DEFAULT                       (_CMU_LFXOCTRL_BUFCUR_DEFAULT << 20)    /**< Shifted mode DEFAULT for CMU_LFXOCTRL */
#define _CMU_LFXOCTRL_TIMEOUT_SHIFT                       24                                      /**< Shift value for CMU_TIMEOUT */
#define _CMU_LFXOCTRL_TIMEOUT_MASK                        0x7000000UL                             /**< Bit mask for CMU_TIMEOUT */
#define _CMU_LFXOCTRL_TIMEOUT_2CYCLES                     0x00000000UL                            /**< Mode 2CYCLES for CMU_LFXOCTRL */
#define _CMU_LFXOCTRL_TIMEOUT_256CYCLES                   0x00000001UL                            /**< Mode 256CYCLES for CMU_LFXOCTRL */
#define _CMU_LFXOCTRL_TIMEOUT_1KCYCLES                    0x00000002UL                            /**< Mode 1KCYCLES for CMU_LFXOCTRL */
#define _CMU_LFXOCTRL_TIMEOUT_2KCYCLES                    0x00000003UL                            /**< Mode 2KCYCLES for CMU_LFXOCTRL */
#define _CMU_LFXOCTRL_TIMEOUT_4KCYCLES                    0x00000004UL                            /**< Mode 4KCYCLES for CMU_LFXOCTRL */
#define _CMU_LFXOCTRL_TIMEOUT_8KCYCLES                    0x00000005UL                            /**< Mode 8KCYCLES for CMU_LFXOCTRL */
#define _CMU_LFXOCTRL_TIMEOUT_16KCYCLES                   0x00000006UL                            /**< Mode 16KCYCLES for CMU_LFXOCTRL */
#define _CMU_LFXOCTRL_TIMEOUT_DEFAULT                     0x00000007UL                            /**< Mode DEFAULT for CMU_LFXOCTRL */
#define _CMU_LFXOCTRL_TIMEOUT_32KCYCLES                   0x00000007UL                            /**< Mode 32KCYCLES for CMU_LFXOCTRL */
#define CMU_LFXOCTRL_TIMEOUT_2CYCLES                      (_CMU_LFXOCTRL_TIMEOUT_2CYCLES << 24)   /**< Shifted mode 2CYCLES for CMU_LFXOCTRL */
#define CMU_LFXOCTRL_TIMEOUT_256CYCLES                    (_CMU_LFXOCTRL_TIMEOUT_256CYCLES << 24) /**< Shifted mode 256CYCLES for CMU_LFXOCTRL */
#define CMU_LFXOCTRL_TIMEOUT_1KCYCLES                     (_CMU_LFXOCTRL_TIMEOUT_1KCYCLES << 24)  /**< Shifted mode 1KCYCLES for CMU_LFXOCTRL */
#define CMU_LFXOCTRL_TIMEOUT_2KCYCLES                     (_CMU_LFXOCTRL_TIMEOUT_2KCYCLES << 24)  /**< Shifted mode 2KCYCLES for CMU_LFXOCTRL */
#define CMU_LFXOCTRL_TIMEOUT_4KCYCLES                     (_CMU_LFXOCTRL_TIMEOUT_4KCYCLES << 24)  /**< Shifted mode 4KCYCLES for CMU_LFXOCTRL */
#define CMU_LFXOCTRL_TIMEOUT_8KCYCLES                     (_CMU_LFXOCTRL_TIMEOUT_8KCYCLES << 24)  /**< Shifted mode 8KCYCLES for CMU_LFXOCTRL */
#define CMU_LFXOCTRL_TIMEOUT_16KCYCLES                    (_CMU_LFXOCTRL_TIMEOUT_16KCYCLES << 24) /**< Shifted mode 16KCYCLES for CMU_LFXOCTRL */
#define CMU_LFXOCTRL_TIMEOUT_DEFAULT                      (_CMU_LFXOCTRL_TIMEOUT_DEFAULT << 24)   /**< Shifted mode DEFAULT for CMU_LFXOCTRL */
#define CMU_LFXOCTRL_TIMEOUT_32KCYCLES                    (_CMU_LFXOCTRL_TIMEOUT_32KCYCLES << 24) /**< Shifted mode 32KCYCLES for CMU_LFXOCTRL */

/* Bit fields for CMU ULFRCOCTRL */
#define _CMU_ULFRCOCTRL_RESETVALUE                        0x00020020UL                            /**< Default value for CMU_ULFRCOCTRL */
#define _CMU_ULFRCOCTRL_MASK                              0x00030C3FUL                            /**< Mask for CMU_ULFRCOCTRL */
#define _CMU_ULFRCOCTRL_TUNING_SHIFT                      0                                       /**< Shift value for CMU_TUNING */
#define _CMU_ULFRCOCTRL_TUNING_MASK                       0x3FUL                                  /**< Bit mask for CMU_TUNING */
#define _CMU_ULFRCOCTRL_TUNING_DEFAULT                    0x00000020UL                            /**< Mode DEFAULT for CMU_ULFRCOCTRL */
#define CMU_ULFRCOCTRL_TUNING_DEFAULT                     (_CMU_ULFRCOCTRL_TUNING_DEFAULT << 0)   /**< Shifted mode DEFAULT for CMU_ULFRCOCTRL */
#define _CMU_ULFRCOCTRL_MODE_SHIFT                        10                                      /**< Shift value for CMU_MODE */
#define _CMU_ULFRCOCTRL_MODE_MASK                         0xC00UL                                 /**< Bit mask for CMU_MODE */
#define _CMU_ULFRCOCTRL_MODE_DEFAULT                      0x00000000UL                            /**< Mode DEFAULT for CMU_ULFRCOCTRL */
#define _CMU_ULFRCOCTRL_MODE_1KHZ                         0x00000000UL                            /**< Mode 1KHZ for CMU_ULFRCOCTRL */
#define _CMU_ULFRCOCTRL_MODE_2KHZ                         0x00000001UL                            /**< Mode 2KHZ for CMU_ULFRCOCTRL */
#define _CMU_ULFRCOCTRL_MODE_4KHZ                         0x00000002UL                            /**< Mode 4KHZ for CMU_ULFRCOCTRL */
#define _CMU_ULFRCOCTRL_MODE_32KHZ                        0x00000003UL                            /**< Mode 32KHZ for CMU_ULFRCOCTRL */
#define CMU_ULFRCOCTRL_MODE_DEFAULT                       (_CMU_ULFRCOCTRL_MODE_DEFAULT << 10)    /**< Shifted mode DEFAULT for CMU_ULFRCOCTRL */
#define CMU_ULFRCOCTRL_MODE_1KHZ                          (_CMU_ULFRCOCTRL_MODE_1KHZ << 10)       /**< Shifted mode 1KHZ for CMU_ULFRCOCTRL */
#define CMU_ULFRCOCTRL_MODE_2KHZ                          (_CMU_ULFRCOCTRL_MODE_2KHZ << 10)       /**< Shifted mode 2KHZ for CMU_ULFRCOCTRL */
#define CMU_ULFRCOCTRL_MODE_4KHZ                          (_CMU_ULFRCOCTRL_MODE_4KHZ << 10)       /**< Shifted mode 4KHZ for CMU_ULFRCOCTRL */
#define CMU_ULFRCOCTRL_MODE_32KHZ                         (_CMU_ULFRCOCTRL_MODE_32KHZ << 10)      /**< Shifted mode 32KHZ for CMU_ULFRCOCTRL */
#define _CMU_ULFRCOCTRL_RESTRIM_SHIFT                     16                                      /**< Shift value for CMU_RESTRIM */
#define _CMU_ULFRCOCTRL_RESTRIM_MASK                      0x30000UL                               /**< Bit mask for CMU_RESTRIM */
#define _CMU_ULFRCOCTRL_RESTRIM_DEFAULT                   0x00000002UL                            /**< Mode DEFAULT for CMU_ULFRCOCTRL */
#define CMU_ULFRCOCTRL_RESTRIM_DEFAULT                    (_CMU_ULFRCOCTRL_RESTRIM_DEFAULT << 16) /**< Shifted mode DEFAULT for CMU_ULFRCOCTRL */
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
