tejeez/geckokapula/gecko_sdk_suite/v2.7/platform/radio/rail_lib/common/rail_features.h

/***************************************************************************//**
 * @file
 * @brief Auxiliary header for the RAIL library. Includes consistent definitions
 *   of features available across different chips.
 *******************************************************************************
 * # License
 * <b>Copyright 2018 Silicon Laboratories Inc. www.silabs.com</b>
 *******************************************************************************
 *
 * SPDX-License-Identifier: Zlib
 *
 * The licensor of this software is Silicon Laboratories Inc.
 *
 * This software is provided 'as-is', without any express or implied
 * warranty. In no event will the authors be held liable for any damages
 * arising from the use of this software.
 *
 * Permission is granted to anyone to use this software for any purpose,
 * including commercial applications, and to alter it and redistribute it
 * freely, subject to the following restrictions:
 *
 * 1. The origin of this software must not be misrepresented; you must not
 *    claim that you wrote the original software. If you use this software
 *    in a product, an acknowledgment in the product documentation would be
 *    appreciated but is not required.
 * 2. Altered source versions must be plainly marked as such, and must not be
 *    misrepresented as being the original software.
 * 3. This notice may not be removed or altered from any source distribution.
 *
 ******************************************************************************/

#ifndef __RAIL_FEATURES_H__
#define __RAIL_FEATURES_H__

#ifdef __cplusplus
extern "C" {
#endif

#include "em_device.h"
#include "rail_types.h"

/**
 * @addtogroup RAIL_API RAIL API
 * @{
 */

/******************************************************************************
 * RAIL Features
 *****************************************************************************/
/**
 * @addtogroup Features
 * @brief Overview of support for various features across hardware platforms.
 *        These defines can be used at compile time to determine which
 *        features are available on your platform. However, keep in mind that
 *        these defines hold true for chip families. Your specific part
 *        may have further restrictions (band limitations, power amplifier
 *        restrictions, and so on) on top of those listed below, for which
 *        runtime RAIL_Supports*() APIs can be used to check availability
 *        on a particular chip (after \ref RAIL_Init() has been called).
 *        In general, an attempt to call an API that is not supported on your
 *        chip family as listed below will result in a
 *        \ref RAIL_STATUS_INVALID_CALL.
 * @{
 */
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
